ChoBeomGyu25/2026ESWContest_free_-/SW/Jetson/preprocessing/lower/dual/undistort/step_d25_v2.py

#!/usr/bin/env python3
# -*- coding: utf-8 -*-
"""
step_d25.py

Reference-free bottom/pants finish evaluator.

This file never opens RoArm serial ports and never sends robot commands.
It combines the YOLO26m bottom-pose engine, segmentation contour derivatives,
convexity defects and pose-relative topology to evaluate:

  1) one coherent waist region,
  2) one expected crotch concavity,
  3) two exposed legs and two visible hems,
  4) pose/geometry-fused eight keypoints,
  5) unexpected macro boundary folds or overlap,
  6) broad contrast-supported internal folds only.

No per-garment normal image or user registration is used. Fine wrinkles, elastic
waist gathers, center-rise seams and ordinary hem lines do not block finish.

Snapshot keys:
  Q / ESC : quit
  SPACE   : force one fresh snapshot and evaluate it
  C       : clear the frozen result
  L       : lock/update Homography from currently detected ArUco markers
  R       : clear Homography in memory
  S       : save current overlay and JSON report

Dependency:
  Keep step_d23_v2.py in the same directory.

Recommended:
  python3 step_d25.py

No-window one-shot snapshot:
  python3 step_d25.py --once --no-window
"""

from __future__ import annotations

import argparse
import collections
import json
import math
import os
import sys
import threading
import time
from dataclasses import dataclass, field
from pathlib import Path
from types import SimpleNamespace
from typing import Any, Deque, Dict, List, Optional, Sequence, Tuple

import cv2
import numpy as np

try:
    import step_d23_v2 as d23
except Exception as exc:  # pragma: no cover - clear runtime error for Jetson use
    raise RuntimeError(
        "step_d25.py requires step_d23_v2.py in the same directory. "
        f"Import failed: {exc!r}"
    ) from exc


STEP_D24_BUILD = "2026-07-17-d25-contour-differential-topology-medium-pose"

STATUS_COLORS = {
    "REJUDGE": (0, 190, 255),
    "NOT_READY_SHAPE": (0, 0, 255),
    "NOT_READY_WRINKLE": (0, 80, 255),
    "READY_PENDING": (0, 220, 220),
    "READY_GOOD_ENOUGH": (0, 210, 0),
}

TIER_COLORS = {
    1: (255, 170, 40),   # blue-ish: allowed fine wrinkle
    2: (0, 165, 255),    # orange
    3: (0, 0, 255),      # red
}


@dataclass
class StabilityEntry:
    timestamp: float
    mask_area_px: float
    mask_center_board: np.ndarray
    pose_axis_deg: float
    valid_kpts: int
    mean_kpt_conf: float


@dataclass
class D24State:
    history: Deque[StabilityEntry]
    ready_streak: int = 0
    evaluation_count: int = 0
    latest_status: str = "REJUDGE"
    latest_report: Dict[str, Any] = field(default_factory=dict)
    latest_obs: Optional[Any] = None
    latest_heat: Optional[Any] = None
    latest_overlay: Optional[np.ndarray] = None
    latest_eval_frame: Optional[np.ndarray] = None
    latest_h: Optional[np.ndarray] = None
    last_eval_started: float = 0.0
    force_evaluate: bool = False
    paused: bool = False

    def reset_temporal(self) -> None:
        self.history.clear()
        self.ready_streak = 0
        self.latest_status = "REJUDGE"
        self.latest_report = {
            "status": "REJUDGE",
            "reason": "temporal history reset",
        }


# -----------------------------------------------------------------------------
# Argument/config construction
# -----------------------------------------------------------------------------

def build_parser() -> argparse.ArgumentParser:
    p = argparse.ArgumentParser(
        description="D24-v6 event snapshot tester: pants shape + real-fold-only finish + waist/gather/center-rise structure ignore; no robot motion"
    )

    # Camera / files.
    p.add_argument("--config", default="dual_roarm_big_table_config.json")
    p.add_argument("--hfile", default="dual_big_table_homography_cache.json")
    p.add_argument("--load-h", dest="load_h", action="store_true", default=True)
    p.add_argument("--no-load-h", dest="load_h", action="store_false")
    p.add_argument("--save-h-on-lock", dest="save_h_on_lock", action="store_true", default=True)
    p.add_argument("--no-save-h-on-lock", dest="save_h_on_lock", action="store_false")
    p.add_argument("--auto-lock", dest="auto_lock", action="store_true", default=True)
    p.add_argument("--no-auto-lock", dest="auto_lock", action="store_false")

    p.add_argument("--camera", type=int, default=0)
    p.add_argument("--width", type=int, default=1280)
    p.add_argument("--height", type=int, default=720)
    p.add_argument("--backend", choices=["auto", "v4l2", "dshow", "any"], default="v4l2")
    p.add_argument("--cam-device", default="")
    p.add_argument("--cam-exposure-abs", type=int, default=35)
    p.add_argument("--cam-gain", type=int, default=5)
    p.add_argument("--cam-no-manual", action="store_true")
    p.add_argument("--cam-auto-adjust", dest="cam_auto_adjust", action="store_true", default=False)
    p.add_argument("--cam-auto-settle-s", type=float, default=0.40)
    p.add_argument("--cam-auto-exposure-min", type=int, default=10)
    p.add_argument("--cam-auto-exposure-max", type=int, default=100)
    p.add_argument("--cam-auto-gain-min", type=int, default=0)
    p.add_argument("--cam-auto-gain-max", type=int, default=20)
    p.add_argument("--warmup-frames", type=int, default=10)
    p.add_argument("--no-window", action="store_true")
    p.add_argument("--once", action="store_true")
    p.add_argument("--image", default="", help="Evaluate one saved image instead of the camera.")
    p.add_argument("--output", default="d25_finish_overlay.jpg")
    p.add_argument("--snapshot-dir", default="d25_finish_samples")
    p.add_argument("--log-jsonl", default="d25_finish_log.jsonl")

    # Models and pose inference.
    p.add_argument(
        "--seg-model",
        default="/workspace/project_train/aruco_test/dual/models/kfashion_yolo26s_seg3_e100_best.engine",
    )
    p.add_argument("--seg-imgsz", type=int, default=640)
    p.add_argument("--seg-conf", type=float, default=0.25)
    p.add_argument(
        "--pose-model",
        default="/workspace/project_train/yolo26/bottom_pose8_yolo26m_e40_best.engine",
    )
    p.add_argument("--pose-imgsz", type=int, default=640)
    p.add_argument("--pose-conf", type=float, default=0.10)
    p.add_argument("--pose-kpt-conf", type=float, default=0.20)
    p.add_argument("--pose-tta", dest="pose_tta", action="store_true", default=True)
    p.add_argument("--no-pose-tta", dest="pose_tta", action="store_false")
    p.add_argument("--angles", default="0,180,90,-90,45,-45")
    p.add_argument("--flip-modes", default="none,h")

    # Staged TTA from D23: fast common orientations, full fallback only if weak.
    p.add_argument("--d23-pose-tta-fast-first", dest="d23_pose_tta_fast_first", action="store_true", default=True)
    p.add_argument("--no-d23-pose-tta-fast-first", dest="d23_pose_tta_fast_first", action="store_false")
    p.add_argument("--d23-pose-tta-fast-angles", default="0,180")
    p.add_argument("--d23-pose-tta-fast-flip-modes", default="none")
    p.add_argument("--d23-pose-tta-fast-min-score", type=float, default=28.0)
    p.add_argument("--d23-pose-tta-fast-min-visible", type=int, default=7)
    p.add_argument("--d23-pose-tta-fast-min-mean-conf", type=float, default=0.32)

    # Pose TTA geometry and mask fallback.
    p.add_argument("--tta-min-waist-width-px", type=float, default=40.0)
    p.add_argument("--tta-max-waist-center-offset-ratio", type=float, default=0.35)
    p.add_argument("--tta-min-waist-to-crotch-ratio", type=float, default=0.35)
    p.add_argument("--tta-max-waist-axis-dot", type=float, default=0.45)
    p.add_argument("--tta-pre-spread-hem-gap-ratio", type=float, default=0.42)
    p.add_argument("--tta-pre-spread-open-angle-deg", type=float, default=22.0)
    p.add_argument("--tta-pre-spread-min-hem-visible", type=int, default=2)
    p.add_argument("--tta-mask-max-outside-px", type=float, default=28.0)
    p.add_argument("--tta-mask-min-inside-ratio", type=float, default=0.60)
    p.add_argument("--tta-require-ok-for-motion", dest="tta_require_ok_for_motion", action="store_true", default=True)
    p.add_argument("--no-tta-require-ok-for-motion", dest="tta_require_ok_for_motion", action="store_false")

    p.add_argument("--pose-grabcut-fallback", dest="pose_grabcut_fallback", action="store_true", default=True)
    p.add_argument("--no-pose-grabcut-fallback", dest="pose_grabcut_fallback", action="store_false")
    p.add_argument("--fallback-mask-min-pose-points", type=int, default=6)
    p.add_argument("--fallback-mask-bbox-pad-px", type=int, default=55)
    p.add_argument("--fallback-mask-seed-radius-px", type=int, default=12)
    p.add_argument("--fallback-mask-seed-line-px", type=int, default=18)
    p.add_argument("--fallback-mask-hull-dilate-px", type=int, default=28)
    p.add_argument("--fallback-mask-grabcut-iters", type=int, default=4)
    p.add_argument("--fallback-mask-close-px", type=int, default=9)
    p.add_argument("--fallback-mask-open-px", type=int, default=3)
    p.add_argument("--fallback-mask-min-area-px", type=float, default=1800.0)
    p.add_argument("--fallback-mask-max-frame-ratio", type=float, default=0.70)
    p.add_argument("--fallback-mask-max-kpt-outside-px", type=float, default=22.0)
    p.add_argument("--fallback-mask-min-inside-points", type=int, default=6)
    p.add_argument("--fallback-mask-min-solidity", type=float, default=0.35)

    # Continuous evaluation and temporal stability.
    p.add_argument("--eval-interval-s", type=float, default=0.75)
    p.add_argument("--burst-frame-count", type=int, default=5)
    p.add_argument("--history-count", type=int, default=3)
    p.add_argument("--ready-confirm-count", type=int, default=2)
    p.add_argument("--min-valid-keypoints", type=int, default=7)
    p.add_argument("--min-mean-kpt-conf", type=float, default=0.45)
    p.add_argument("--stable-mask-area-rel", type=float, default=0.05)
    p.add_argument("--stable-center-shift-mm", type=float, default=8.0)
    p.add_argument("--stable-pose-axis-spread-deg", type=float, default=6.0)

    # Base heatmap.
    p.add_argument("--wrinkle-heatmap-mode", dest="wrinkle_heatmap_mode", action="store_true", default=True)
    p.add_argument("--no-wrinkle-heatmap-mode", dest="wrinkle_heatmap_mode", action="store_false")
    p.add_argument("--wrinkle-heatmap-draw", dest="wrinkle_heatmap_draw", action="store_true", default=True)
    p.add_argument("--no-wrinkle-heatmap-draw", dest="wrinkle_heatmap_draw", action="store_false")
    p.add_argument("--wrinkle-heatmap-alpha", type=float, default=0.30)
    p.add_argument("--wrinkle-heatmap-clahe-clip", type=float, default=2.0)
    p.add_argument("--wrinkle-heatmap-clahe-tile", type=int, default=8)
    p.add_argument("--wrinkle-heatmap-blur-ksize", type=int, default=41)
    p.add_argument("--wrinkle-heatmap-erode-px", type=int, default=12)
    p.add_argument("--wrinkle-heatmap-percentile", type=float, default=93.0)
    p.add_argument("--wrinkle-heatmap-min-blob-area", type=float, default=45.0)
    p.add_argument("--wrinkle-heatmap-max-candidates", type=int, default=12)
    p.add_argument("--wrinkle-heatmap-gabor", dest="wrinkle_heatmap_gabor", action="store_true", default=True)
    p.add_argument("--no-wrinkle-heatmap-gabor", dest="wrinkle_heatmap_gabor", action="store_false")
    p.add_argument("--wrinkle-heatmap-gabor-ksize", type=int, default=17)
    p.add_argument("--wrinkle-heatmap-gabor-lambda", type=float, default=8.0)
    p.add_argument("--wrinkle-heatmap-gabor-sigma", type=float, default=4.0)
    p.add_argument("--wrinkle-heatmap-score-min", type=float, default=35.0)

    # D24 robust response guard. This supplements P93 rather than allowing P93 alone.
    p.add_argument("--d24-robust-k", type=float, default=2.7)
    p.add_argument("--d24-robust-score-min", type=float, default=35.0)
    p.add_argument("--d24-candidate-min-robust-support", type=float, default=0.10)

    # Natural structure ignore zones.
    p.add_argument("--d19-ignore-waistband-wrinkles", dest="d19_ignore_waistband_wrinkles", action="store_true", default=True)
    p.add_argument("--no-d19-ignore-waistband-wrinkles", dest="d19_ignore_waistband_wrinkles", action="store_false")
    p.add_argument("--d19-waistband-back-mm", type=float, default=18.0)
    p.add_argument("--d19-waistband-forward-mm", type=float, default=72.0)
    p.add_argument("--d19-waistband-side-expand-mm", type=float, default=28.0)
    p.add_argument("--d23-waistband-forward-ratio", type=float, default=0.70)
    p.add_argument("--d23-waistband-forward-max-mm", type=float, default=95.0)
    p.add_argument("--d23-waist-structure-veto", dest="d23_waist_structure_veto", action="store_true", default=True)
    p.add_argument("--no-d23-waist-structure-veto", dest="d23_waist_structure_veto", action="store_false")
    p.add_argument("--d23-waist-structure-back-mm", type=float, default=22.0)
    p.add_argument("--d23-waist-structure-forward-mm", type=float, default=78.0)
    p.add_argument("--d23-waist-structure-forward-ratio", type=float, default=0.70)
    p.add_argument("--d23-waist-structure-forward-max-mm", type=float, default=98.0)
    p.add_argument("--d23-waist-structure-side-expand-mm", type=float, default=32.0)
    p.add_argument("--d23-waist-structure-parallel-deg", type=float, default=25.0)
    p.add_argument("--d23-waist-structure-min-length-mm", type=float, default=35.0)
    p.add_argument("--d23-waist-structure-min-length-ratio", type=float, default=0.22)
    p.add_argument("--d23-pre-veto-candidate-multiplier", type=int, default=3)
    p.add_argument("--d23-draw-waist-veto", dest="d23_draw_waist_veto", action="store_true", default=True)
    p.add_argument("--no-d23-draw-waist-veto", dest="d23_draw_waist_veto", action="store_false")

    p.add_argument("--d19-ignore-crotch-wrinkles", dest="d19_ignore_crotch_wrinkles", action="store_true", default=True)
    p.add_argument("--no-d19-ignore-crotch-wrinkles", dest="d19_ignore_crotch_wrinkles", action="store_false")
    p.add_argument("--d19-crotch-axial-radius-mm", type=float, default=56.0)
    p.add_argument("--d19-crotch-lateral-radius-mm", type=float, default=66.0)
    p.add_argument("--d19-crotch-forward-shift-mm", type=float, default=10.0)

    # Conditional seam veto: do not erase the entire side/hem area; require line agreement.
    p.add_argument("--d24-seam-veto", dest="d24_seam_veto", action="store_true", default=True)
    p.add_argument("--no-d24-seam-veto", dest="d24_seam_veto", action="store_false")
    p.add_argument("--d24-seam-band-mm", type=float, default=18.0)
    p.add_argument("--d24-seam-parallel-deg", type=float, default=24.0)
    p.add_argument("--d24-seam-min-linearity", type=float, default=3.0)
    p.add_argument("--d24-seam-min-length-mm", type=float, default=30.0)
    p.add_argument("--d24-seam-min-support-ratio", type=float, default=0.70)
    p.add_argument("--d24-seam-max-sample-points", type=int, default=1800)

    # D20 meaningful wrinkle classification.
    p.add_argument("--d20-require-dark-shadow", dest="d20_require_dark_shadow", action="store_true", default=True)
    p.add_argument("--no-d20-require-dark-shadow", dest="d20_require_dark_shadow", action="store_false")
    p.add_argument("--d20-ignore-fine-wrinkles", dest="d20_ignore_fine_wrinkles", action="store_true", default=True)
    p.add_argument("--no-d20-ignore-fine-wrinkles", dest="d20_ignore_fine_wrinkles", action="store_false")
    p.add_argument("--d20-shadow-blur-ksize", type=int, default=51)
    p.add_argument("--d20-shadow-min-scale-raw", type=float, default=8.0)
    p.add_argument("--d20-shadow-support-raw-min", type=float, default=3.0)
    p.add_argument("--d20-hard-min-component-area-px", type=float, default=70.0)

    # T3 strong criteria.
    p.add_argument("--d20-strong-area-px", type=float, default=240.0)
    p.add_argument("--d20-strong-area-ratio", type=float, default=0.015)
    p.add_argument("--d20-strong-length-mm", type=float, default=80.0)
    p.add_argument("--d20-strong-length-px", type=float, default=95.0)
    p.add_argument("--d20-strong-dark-mean", type=float, default=38.0)
    p.add_argument("--d20-strong-dark-max", type=float, default=105.0)
    p.add_argument("--d20-strong-dark-support", type=float, default=0.10)

    # T2 medium criteria.
    p.add_argument("--d20-medium-area-px", type=float, default=150.0)
    p.add_argument("--d20-medium-area-ratio", type=float, default=0.005)
    p.add_argument("--d20-medium-length-mm", type=float, default=45.0)
    p.add_argument("--d20-medium-length-px", type=float, default=58.0)
    p.add_argument("--d20-medium-dark-mean", type=float, default=20.0)
    p.add_argument("--d20-medium-dark-max", type=float, default=65.0)
    p.add_argument("--d20-medium-dark-support", type=float, default=0.06)

    # D21 candidate severity / T1 allowance.
    p.add_argument("--d21v4-action-min-tier", type=int, default=2)
    p.add_argument("--d21v4-action-severity-override", type=float, default=0.55)
    p.add_argument("--d21v4-good-enough-finish", dest="d21v4_good_enough_finish", action="store_true", default=True)
    p.add_argument("--d21-severity-length-ref-mm", type=float, default=120.0)
    p.add_argument("--d21-severity-area-ref-px", type=float, default=550.0)
    p.add_argument("--d21-severity-dark-ref", type=float, default=60.0)
    p.add_argument("--d21-severity-dark-max-ref", type=float, default=160.0)
    p.add_argument("--d21-severity-sagitta-ref-mm", type=float, default=45.0)
    p.add_argument("--d21-pull-min-mm", type=float, default=25.0)
    p.add_argument("--d21-pull-max-mm", type=float, default=95.0)

    # Shape thresholds from the agreed algorithm.
    p.add_argument("--finish-shape-score-min", type=float, default=0.75)
    p.add_argument("--finish-hem-gap-ratio-min", type=float, default=0.55)
    p.add_argument("--finish-hem-gap-ratio-max", type=float, default=1.35)
    p.add_argument("--finish-leg-balance-min", type=float, default=0.82)
    p.add_argument("--finish-waist-center-offset-max", type=float, default=0.15)
    p.add_argument("--finish-waist-line-error-max", type=float, default=0.16)
    p.add_argument("--finish-crotch-axis-offset-max", type=float, default=0.22)
    p.add_argument("--finish-axis-to-waist-min", type=float, default=0.75)

    # Lower silhouette thresholds.
    p.add_argument("--d22-require-lower-leg-symmetry", dest="d22_require_lower_leg_symmetry", action="store_true", default=True)
    p.add_argument("--no-d22-require-lower-leg-symmetry", dest="d22_require_lower_leg_symmetry", action="store_false")
    p.add_argument("--d22-symmetry-axis-min-mm", type=float, default=35.0)
    p.add_argument("--d22-symmetry-lower-start-mm", type=float, default=-4.0)
    p.add_argument("--d22-symmetry-ignore-axis-band-mm", type=float, default=5.0)
    p.add_argument("--d22-symmetry-grid-mm", type=float, default=4.0)
    p.add_argument("--d22-symmetry-grid-close-cells", type=int, default=1)
    p.add_argument("--d22-symmetry-band-count", type=int, default=6)
    p.add_argument("--d22-symmetry-min-points-per-band", type=int, default=60)
    p.add_argument("--d22-symmetry-max-sample-points", type=int, default=100000)
    p.add_argument("--d22-lower-reflected-iou-min", type=float, default=0.68)
    p.add_argument("--d22-lower-width-balance-median-min", type=float, default=0.75)
    p.add_argument("--d22-lower-width-balance-min-min", type=float, default=0.60)
    p.add_argument("--d22-lower-profile-error-p90-max", type=float, default=0.38)
    p.add_argument("--d22-lower-side-area-balance-min", type=float, default=0.74)
    p.add_argument("--d22-hem-axis-balance-min", type=float, default=0.74)
    p.add_argument("--d22-leg-length-balance-min", type=float, default=0.82)
    p.add_argument("--d22-symmetry-score-min", type=float, default=0.70)

    # D24-v2 final policy: pants shape is mandatory, but only clearly major
    # wrinkles block READY. T1/T2 counts and total active ratio are diagnostic only.
    p.add_argument("--finish-max-t3-count", type=int, default=0)
    p.add_argument("--finish-max-t2-count", type=int, default=999)  # display/compatibility only
    p.add_argument("--finish-max-severity", type=float, default=1.0)  # display/compatibility only
    p.add_argument("--finish-actionable-ratio", type=float, default=1.0)  # diagnostic only
    p.add_argument("--finish-max-blob-ratio", type=float, default=1.0)  # diagnostic only

    # Waistline-relative fine-wrinkle allowance. A candidate smaller/weaker than
    # the detected waistband structure is explicitly marked as allowed.
    p.add_argument("--d24v2-waist-relative-enable", dest="d24v2_waist_relative_enable", action="store_true", default=True)
    p.add_argument("--no-d24v2-waist-relative-enable", dest="d24v2_waist_relative_enable", action="store_false")
    p.add_argument("--d24v2-waist-length-ratio-ignore", type=float, default=0.40)
    p.add_argument("--d24v2-waist-area-ratio-ignore", type=float, default=0.30)
    p.add_argument("--d24v2-waist-response-ratio-ignore", type=float, default=0.85)
    p.add_argument("--d24v2-waist-ref-back-mm", type=float, default=18.0)
    p.add_argument("--d24v2-waist-ref-forward-mm", type=float, default=72.0)
    p.add_argument("--d24v2-waist-ref-side-expand-mm", type=float, default=28.0)
    p.add_argument("--d24v2-waist-ref-parallel-deg", type=float, default=30.0)
    p.add_argument("--d24v2-waist-ref-min-length-ratio", type=float, default=0.25)
    p.add_argument("--d24v2-waist-ref-min-area-px", type=float, default=45.0)
    p.add_argument("--d24v2-waist-ref-threshold-scale", type=float, default=0.78)

    # Absolute major-wrinkle overrides. These block READY even when the candidate
    # is smaller than the waistband reference.
    p.add_argument("--d24v2-major-length-mm", type=float, default=80.0)
    p.add_argument("--d24v2-major-area-ratio", type=float, default=0.015)
    p.add_argument("--d24v2-major-severity", type=float, default=0.60)
    p.add_argument("--d24v2-major-severity-min-length-mm", type=float, default=60.0)
    p.add_argument("--d24v2-major-waist-span-ratio", type=float, default=0.50)
    p.add_argument("--d24v2-major-waist-span-min-area-ratio", type=float, default=0.005)

    # D24-v5: waistband-connected radial gathers are natural elastic-waist structures.
    p.add_argument("--d24v5-waist-gather-ignore", dest="d24v5_waist_gather_ignore", action="store_true", default=True)
    p.add_argument("--no-d24v5-waist-gather-ignore", dest="d24v5_waist_gather_ignore", action="store_false")
    p.add_argument("--d24v5-waist-gather-depth-ratio", type=float, default=0.45,
                   help="Maximum gather depth as a fraction of waist-to-crotch distance.")
    p.add_argument("--d24v5-waist-gather-depth-max-mm", type=float, default=105.0)
    p.add_argument("--d24v5-waist-gather-connect-mm", type=float, default=22.0,
                   help="Allowed gap from the existing waistband ignore boundary.")
    p.add_argument("--d24v5-waist-gather-radial-angle-deg", type=float, default=32.0)
    p.add_argument("--d24v5-waist-gather-max-length-ratio", type=float, default=0.35)
    p.add_argument("--d24v5-waist-gather-max-length-mm", type=float, default=78.0)
    p.add_argument("--d24v5-waist-gather-max-area-ratio", type=float, default=0.012)
    p.add_argument("--d24v5-waist-gather-side-expand-mm", type=float, default=20.0)
    p.add_argument("--d24v5-waist-gather-min-upper-support", type=float, default=0.70)

    # D24-v5: fine wrinkles never block finish. Only broad/deep fold-like components do.
    p.add_argument("--d24v5-fold-min-length-mm", type=float, default=75.0)
    p.add_argument("--d24v5-fold-min-width-mm", type=float, default=7.0)
    p.add_argument("--d24v5-fold-min-area-ratio", type=float, default=0.0045)
    p.add_argument("--d24v5-fold-min-severity", type=float, default=0.45)
    p.add_argument("--d24v5-fold-min-mean-response", type=float, default=75.0)
    p.add_argument("--d24v5-fold-broad-min-length-mm", type=float, default=45.0)
    p.add_argument("--d24v5-fold-broad-min-width-mm", type=float, default=13.0)
    p.add_argument("--d24v5-fold-broad-min-area-ratio", type=float, default=0.0075)
    p.add_argument("--d24v5-fold-large-area-ratio", type=float, default=0.018)
    p.add_argument("--d24v5-draw-allowed-fine", dest="d24v5_draw_allowed_fine", action="store_true", default=False)
    p.add_argument("--no-d24v5-draw-allowed-fine", dest="d24v5_draw_allowed_fine", action="store_false")

    # D24-v6: pose-relative front/center-rise seam from waist center toward crotch.
    # This narrow structure band is erased BEFORE CCA so a bright seam cannot merge
    # with nearby waistband gathers and become one large false fold component.
    p.add_argument("--d24v6-center-rise-ignore", dest="d24v6_center_rise_ignore", action="store_true", default=True)
    p.add_argument("--no-d24v6-center-rise-ignore", dest="d24v6_center_rise_ignore", action="store_false")
    p.add_argument("--d24v6-center-rise-half-width-mm", type=float, default=18.0)
    p.add_argument("--d24v6-center-rise-start-mm", type=float, default=48.0,
                   help="Distance below waist center where the narrow center-rise seam mask starts.")
    p.add_argument("--d24v6-center-rise-end-before-crotch-mm", type=float, default=0.0)
    p.add_argument("--d24v6-center-rise-end-expand-mm", type=float, default=12.0)

    # D24-v6 color-robust fold gate. A large normalized heatmap component alone is
    # no longer a blocker; broad geometry must also have real local intensity contrast.
    p.add_argument("--d24v6-fold-min-abs-contrast", type=float, default=7.0,
                   help="Minimum mean absolute high-pass contrast in original gray levels.")
    p.add_argument("--d24v6-fold-min-contrast-support", type=float, default=0.28,
                   help="Minimum fraction of component pixels above the absolute-contrast pixel threshold.")
    p.add_argument("--d24v6-fold-contrast-pixel-threshold", type=float, default=8.0)
    p.add_argument("--d24v6-fold-extreme-width-mm", type=float, default=22.0)
    p.add_argument("--d24v6-fold-extreme-area-ratio", type=float, default=0.016)

    # D24-v4 event-driven snapshot gate. The camera remains live, but heavy
    # pose/segmentation/heatmap inference runs only after a confirmed scene change
    # followed by a stillness interval.
    p.add_argument("--auto-snapshot-on-change", dest="auto_snapshot_on_change", action="store_true", default=True)
    p.add_argument("--no-auto-snapshot-on-change", dest="auto_snapshot_on_change", action="store_false")
    p.add_argument("--startup-auto-snapshot", dest="startup_auto_snapshot", action="store_true", default=True)
    p.add_argument("--no-startup-auto-snapshot", dest="startup_auto_snapshot", action="store_false")
    p.add_argument("--change-mean-threshold", type=float, default=3.5,
                   help="Brightness-compensated mean board difference needed to arm a new snapshot.")
    p.add_argument("--change-pixel-threshold", type=float, default=12.0,
                   help="Per-pixel difference used to calculate changed-area ratio.")
    p.add_argument("--change-active-ratio", type=float, default=0.018,
                   help="Fraction of board pixels that must change when mean difference alone is small.")
    p.add_argument("--change-min-frames", type=int, default=3,
                   help="Consecutive changed frames required before waiting for stillness.")
    p.add_argument("--change-cooldown-s", type=float, default=0.60,
                   help="Ignore change triggers briefly after each completed snapshot.")
    p.add_argument("--change-board-shrink-px", type=int, default=10,
                   help="Ignore a narrow band at the ArUco board boundary during change detection.")
    p.add_argument("--change-preview-width", type=int, default=160)
    p.add_argument("--change-preview-height", type=int, default=90)
    p.add_argument("--settle-motion-threshold", type=float, default=2.5,
                   help="Frame-to-frame mean difference below which the pants are considered still.")
    p.add_argument("--settle-seconds", type=float, default=0.80,
                   help="How long the view must remain still before automatic snapshot inference.")
    p.add_argument("--settle-min-frames", type=int, default=5)
    p.add_argument("--capture-flush-frames", type=int, default=2)
    p.add_argument("--pause-auto", dest="pause_auto", action="store_true", default=False)

    p.add_argument("--panel-width", type=int, default=680)
    p.add_argument("--window-name", default="D25_PANTS_TOPOLOGY_FINISH")
    return p


def finalize_args(args: argparse.Namespace) -> argparse.Namespace:
    args.pose_tta_angles_list = d23.parse_pose_tta_angles(args.angles)
    args.pose_tta_flip_modes_list = d23.parse_pose_tta_flip_modes(args.flip_modes)

    # Names expected by D23 shape helpers.
    args.d19_finish_require_shape = True
    args.d19_finish_shape_score_good = float(args.finish_shape_score_min)
    args.d19_finish_shape_hem_gap_ratio_min = float(args.finish_hem_gap_ratio_min)
    args.d19_finish_shape_hem_gap_ratio_max = float(args.finish_hem_gap_ratio_max)
    args.d19_finish_shape_leg_balance_min = float(args.finish_leg_balance_min)
    args.d19_finish_shape_waist_center_offset_max = float(args.finish_waist_center_offset_max)
    args.d19_finish_shape_waist_line_error_max = float(args.finish_waist_line_error_max)
    args.d19_finish_shape_crotch_axis_offset_max = float(args.finish_crotch_axis_offset_max)
    args.d19_finish_shape_axis_to_waist_min = float(args.finish_axis_to_waist_min)

    # Geometry helper defaults that are accessed directly in a few old functions.
    args.d21_curve_min_inlier_ratio = 0.62
    args.d21_curve_max_residual_mm = 8.0
    args.d21_curve_min_sagitta_mm = 10.0
    args.d21_curve_min_arc_length_mm = 50.0
    args.d21_curve_min_radius_mm = 25.0
    args.d21_curve_max_radius_mm = 900.0
    args.d21_curve_vs_line_error_ratio = 0.90
    args.d21_line_max_residual_mm = 8.0
    args.d21_line_max_sagitta_mm = 10.0
    args.d21_circle_ransac_iters = 120
    args.d21_circle_inlier_tol_mm = 7.0
    args.d21_fit_max_points = 220
    args.d21_track_match_distance_mm = 35.0
    args.d21_static_required_actions = 999999  # No automatic structural learning in D24.
    args.d21v3_static_require_fine = True
    args.d21v3_static_max_tier = 1
    args.d21v3_static_max_severity = 0.45
    args.d21v3_static_max_length_mm = 65.0
    args.d21v3_static_max_area_px = 240.0
    args.d21v3_static_max_dark_mean = 38.0
    return args


# -----------------------------------------------------------------------------
# Geometry / temporal stability
# -----------------------------------------------------------------------------

def angle_diff_180(a_deg: float, b_deg: float) -> float:
    return abs((float(a_deg) - float(b_deg) + 90.0) % 180.0 - 90.0)


def pose_axis_angle(obs: Any) -> float:
    if obs is None or obs.pose is None:
        return 0.0
    v = np.asarray(obs.pose.lower_center, np.float32) - np.asarray(obs.pose.waist_center, np.float32)
    return float(math.degrees(math.atan2(float(v[1]), float(v[0]))))


def observation_entry(obs: Any) -> StabilityEntry:
    confs = list(obs.pose.keypoint_conf.values()) if obs and obs.pose else []
    return StabilityEntry(
        timestamp=time.time(),
        mask_area_px=float(obs.mask.area_px),
        mask_center_board=np.asarray(obs.mask.center_board, np.float32).reshape(2),
        pose_axis_deg=pose_axis_angle(obs),
        valid_kpts=len(confs),
        mean_kpt_conf=float(np.mean(confs)) if confs else 0.0,
    )


def temporal_stability_report(history: Sequence[StabilityEntry], args) -> Dict[str, Any]:
    need = max(2, int(args.history_count))
    if len(history) < need:
        return {
            "good": False,
            "reason": f"history {len(history)}/{need}",
            "history_count": len(history),
            "required": need,
        }

    entries = list(history)[-need:]
    areas = np.asarray([e.mask_area_px for e in entries], np.float32)
    centers = np.asarray([e.mask_center_board for e in entries], np.float32)
    angles = [e.pose_axis_deg for e in entries]

    med_area = float(np.median(areas))
    area_rel = float(np.max(np.abs(areas - med_area)) / max(1.0, med_area))
    med_center = np.median(centers, axis=0)
    center_shift = float(np.max(np.linalg.norm(centers - med_center.reshape(1, 2), axis=1)))
    angle_spread = max(angle_diff_180(a, b) for a in angles for b in angles)

    checks = {
        "mask_area": area_rel <= float(args.stable_mask_area_rel),
        "mask_center": center_shift <= float(args.stable_center_shift_mm),
        "pose_axis": angle_spread <= float(args.stable_pose_axis_spread_deg),
    }
    return {
        "good": bool(all(checks.values())),
        "reason": "OK" if all(checks.values()) else "observation changed",
        "checks": checks,
        "history_count": len(entries),
        "mask_area_rel": area_rel,
        "center_shift_mm": center_shift,
        "pose_axis_spread_deg": float(angle_spread),
        "limits": {
            "mask_area_rel": float(args.stable_mask_area_rel),
            "center_shift_mm": float(args.stable_center_shift_mm),
            "pose_axis_spread_deg": float(args.stable_pose_axis_spread_deg),
        },
    }


# -----------------------------------------------------------------------------
# Conditional side/inner/hem seam filtering
# -----------------------------------------------------------------------------

def point_segment_distances(points: np.ndarray, a: np.ndarray, b: np.ndarray) -> np.ndarray:
    pts = np.asarray(points, np.float32).reshape(-1, 2)
    a = np.asarray(a, np.float32).reshape(2)
    b = np.asarray(b, np.float32).reshape(2)
    ab = b - a
    denom = float(np.dot(ab, ab))
    if denom < 1e-8:
        return np.linalg.norm(pts - a.reshape(1, 2), axis=1)
    t = np.clip(((pts - a.reshape(1, 2)) @ ab) / denom, 0.0, 1.0)
    proj = a.reshape(1, 2) + t[:, None] * ab.reshape(1, 2)
    return np.linalg.norm(pts - proj, axis=1)


def expected_seam_segments(obs: Any) -> List[Dict[str, Any]]:
    if obs is None or obs.pose is None:
        return []
    kb = obs.pose.keypoints_board
    segments: List[Dict[str, Any]] = []

    def add(name: str, n1: str, n2: str) -> None:
        if n1 in kb and n2 in kb:
            a = np.asarray(kb[n1], np.float32)
            b = np.asarray(kb[n2], np.float32)
            if float(np.linalg.norm(b - a)) >= 12.0:
                segments.append({"name": name, "a": a, "b": b})

    add("LEFT_OUTER_SEAM", "waist_img_left", "img_left_hem_outer")
    add("RIGHT_OUTER_SEAM", "waist_img_right", "img_right_hem_outer")
    add("LEFT_INNER_SEAM", "crotch", "img_left_hem_inner")
    add("RIGHT_INNER_SEAM", "crotch", "img_right_hem_inner")
    add("LEFT_HEM", "img_left_hem_outer", "img_left_hem_inner")
    add("RIGHT_HEM", "img_right_hem_inner", "img_right_hem_outer")
    return segments


def candidate_component_mask(heat: Any, cand: Dict[str, Any]) -> Optional[np.ndarray]:
    binary = getattr(heat, "d21v4_residual_binary", None)
    if not isinstance(binary, np.ndarray):
        binary = getattr(heat, "binary", None)
    if not isinstance(binary, np.ndarray):
        return None
    n, labels = cv2.connectedComponents((binary > 0).astype(np.uint8), connectivity=8)
    cx, cy = [int(round(float(v))) for v in cand.get("center_px", [0.0, 0.0])]
    cx = int(np.clip(cx, 0, labels.shape[1] - 1))
    cy = int(np.clip(cy, 0, labels.shape[0] - 1))
    lid = int(labels[cy, cx])
    if lid <= 0 or lid >= n:
        # Search within the candidate bbox if its center fell in a morphology hole.
        x, y, w, h = [int(v) for v in cand.get("bbox", [0, 0, 0, 0])]
        roi = labels[max(0, y):min(labels.shape[0], y + h), max(0, x):min(labels.shape[1], x + w)]
        vals, counts = np.unique(roi[roi > 0], return_counts=True)
        if len(vals) == 0:
            return None
        lid = int(vals[int(np.argmax(counts))])
    return ((labels == lid).astype(np.uint8) * 255)


def component_board_points(component: np.ndarray, H: np.ndarray, max_points: int) -> np.ndarray:
    ys, xs = np.where(component > 0)
    pts = np.column_stack([xs, ys]).astype(np.float32)
    if len(pts) > max_points:
        step = max(1, int(math.ceil(len(pts) / float(max_points))))
        pts = pts[::step]
    if len(pts) == 0:
        return np.empty((0, 2), np.float32)
    return cv2.perspectiveTransform(pts.reshape(-1, 1, 2), H).reshape(-1, 2)


def axis_angle_error_deg(v1: np.ndarray, v2: np.ndarray) -> float:
    a = np.asarray(v1, np.float32).reshape(2)
    b = np.asarray(v2, np.float32).reshape(2)
    na, nb = float(np.linalg.norm(a)), float(np.linalg.norm(b))
    if na < 1e-6 or nb < 1e-6:
        return 180.0
    c = float(np.clip(abs(np.dot(a / na, b / nb)), 0.0, 1.0))
    return float(math.degrees(math.acos(c)))


def seam_veto_report(cand: Dict[str, Any], heat: Any, obs: Any, H: np.ndarray, args) -> Dict[str, Any]:
    out: Dict[str, Any] = {"matched": False, "name": "", "reason": "not a seam"}
    if not bool(args.d24_seam_veto):
        return out

    length = float(cand.get("major_length_mm", 0.0))
    linearity = float(cand.get("linearity", 1.0))
    if length < float(args.d24_seam_min_length_mm) or linearity < float(args.d24_seam_min_linearity):
        return {**out, "reason": "short or non-linear"}

    comp = candidate_component_mask(heat, cand)
    if comp is None:
        return {**out, "reason": "component unavailable"}
    pts = component_board_points(comp, H, max(100, int(args.d24_seam_max_sample_points)))
    if len(pts) < 8:
        return {**out, "reason": "too few component points"}

    geom = cand.get("d21_geometry", {}) or {}
    tangent = geom.get("tangent_board")
    if tangent is None:
        center_px = cand.get("center_px", [0.0, 0.0])
        tangent = d23._pixel_axis_to_board(H, center_px, cand.get("major_axis_px", [1.0, 0.0]))
    if tangent is None:
        return {**out, "reason": "axis unavailable"}
    tangent = np.asarray(tangent, np.float32)

    best = None
    for seg in expected_seam_segments(obs):
        seg_vec = np.asarray(seg["b"], np.float32) - np.asarray(seg["a"], np.float32)
        angle_error = axis_angle_error_deg(tangent, seg_vec)
        dists = point_segment_distances(pts, seg["a"], seg["b"])
        support = float(np.count_nonzero(dists <= float(args.d24_seam_band_mm))) / float(max(1, len(dists)))
        score = support - 0.005 * angle_error
        item = {
            "name": seg["name"],
            "support_ratio": support,
            "parallel_error_deg": angle_error,
            "score": score,
            "a": [float(seg["a"][0]), float(seg["a"][1])],
            "b": [float(seg["b"][0]), float(seg["b"][1])],
        }
        if best is None or score > float(best["score"]):
            best = item

    if best is None:
        return out
    matched = bool(
        float(best["support_ratio"]) >= float(args.d24_seam_min_support_ratio)
        and float(best["parallel_error_deg"]) <= float(args.d24_seam_parallel_deg)
    )
    return {
        **best,
        "matched": matched,
        "reason": "pose-relative seam" if matched else "seam agreement insufficient",
        "length_mm": length,
        "linearity": linearity,
    }


# -----------------------------------------------------------------------------
# D24 robust heat support and final evaluation
# -----------------------------------------------------------------------------

def robust_heat_threshold(heat: Any, args) -> Dict[str, float]:
    if heat is None:
        return {"threshold": 255.0, "median": 0.0, "mad": 0.0, "sigma": 0.0}
    values = heat.heatmap[heat.inner_mask > 0].astype(np.float32)
    if values.size == 0:
        return {"threshold": 255.0, "median": 0.0, "mad": 0.0, "sigma": 0.0}
    med = float(np.median(values))
    mad = float(np.median(np.abs(values - med)))
    sigma = max(1.0, 1.4826 * mad)
    threshold = max(float(args.d24_robust_score_min), med + float(args.d24_robust_k) * sigma)
    return {"threshold": threshold, "median": med, "mad": mad, "sigma": sigma}


def candidate_robust_support(cand: Dict[str, Any], heat: Any, threshold: float) -> float:
    comp = candidate_component_mask(heat, cand)
    if comp is None:
        return 0.0
    vals = heat.heatmap[comp > 0]
    if vals.size == 0:
        return 0.0
    return float(np.count_nonzero(vals.astype(np.float32) >= float(threshold))) / float(vals.size)


def observation_quality_report(obs: Any, args) -> Dict[str, Any]:
    if obs is None or obs.mask is None or obs.pose is None:
        return {
            "good": False,
            "reason": "pose or mask missing",
            "valid_keypoints": 0,
            "mean_kpt_conf": 0.0,
        }
    confs = list(obs.pose.keypoint_conf.values())
    valid_kpts = len(confs)
    mean_conf = float(np.mean(confs)) if confs else 0.0
    checks = {
        "observation_valid": bool(obs.valid),
        "pose_valid": bool(obs.pose.valid),
        "mask_area": float(obs.mask.area_px) >= 1200.0,
        "valid_keypoints": valid_kpts >= int(args.min_valid_keypoints),
        "mean_kpt_conf": mean_conf >= float(args.min_mean_kpt_conf),
    }
    return {
        "good": bool(all(checks.values())),
        "reason": "OK" if all(checks.values()) else "observation quality low",
        "checks": checks,
        "valid_keypoints": valid_kpts,
        "mean_kpt_conf": mean_conf,
        "pose_tta_state": str(obs.pose.tta_state),
        "pose_tta_score": float(obs.pose.tta_score),
        "pose_tta_tested": int(obs.pose.tta_tested_count),
        "mask_area_px": float(obs.mask.area_px),
    }


def _d24v2_waist_reference(obs: Any, heat: Any, H: np.ndarray, robust: Dict[str, float], args) -> Dict[str, Any]:
    """Measure a visible waistband structural response as a per-garment ruler.

    D23 already removes pose-known waistband candidates from robot/finish
    candidates. D24-v2 independently samples the raw heatmap inside a narrow
    pose-relative waistband band, so small residual wrinkles can be compared
    with the garment's own natural waistband response.
    """
    out: Dict[str, Any] = {
        "valid": False,
        "reason": "waist reference unavailable",
        "length_mm": 0.0,
        "area_px": 0.0,
        "mean_response": 0.0,
        "max_response": 0.0,
        "waist_width_mm": 0.0,
        "component_count": 0,
    }
    if not bool(getattr(args, "d24v2_waist_relative_enable", True)):
        out["reason"] = "disabled"
        return out
    if obs is None or obs.pose is None or not obs.pose.valid or heat is None or H is None:
        return out

    p = obs.pose
    wl = np.asarray(p.waist_left, np.float32)
    wc = np.asarray(p.waist_center, np.float32)
    wr = np.asarray(p.waist_right, np.float32)
    lower = np.asarray(p.lower_center, np.float32)
    body_u = d23._safe_unit(lower - wc)
    waist_u = d23._safe_unit(wr - wl)
    if abs(float(np.dot(body_u, waist_u))) > 0.55:
        waist_u = np.asarray([-body_u[1], body_u[0]], np.float32)

    waist_width = max(1.0, float(np.linalg.norm(wr - wl)))
    half_width = 0.5 * waist_width + float(args.d24v2_waist_ref_side_expand_mm)
    back = max(0.0, float(args.d24v2_waist_ref_back_mm))
    forward = max(0.0, float(args.d24v2_waist_ref_forward_mm))
    corners = [
        wc - waist_u * half_width - body_u * back,
        wc + waist_u * half_width - body_u * back,
        wc + waist_u * half_width + body_u * forward,
        wc - waist_u * half_width + body_u * forward,
    ]
    band = d23._d19_board_polygon_to_mask(H, corners, heat.heatmap.shape)
    band = cv2.bitwise_and((band > 0).astype(np.uint8) * 255, (heat.inner_mask > 0).astype(np.uint8) * 255)
    out["waist_width_mm"] = waist_width
    out["band_area_px"] = int(cv2.countNonZero(band))
    if cv2.countNonZero(band) < 30:
        out["reason"] = "waist band too small"
        return out

    threshold = max(
        20.0,
        float(robust.get("threshold", 255.0)) * float(args.d24v2_waist_ref_threshold_scale),
    )
    binary = np.zeros_like(heat.heatmap, np.uint8)
    binary[(heat.heatmap.astype(np.float32) >= threshold) & (band > 0)] = 255
    binary = cv2.morphologyEx(binary, cv2.MORPH_CLOSE, np.ones((5, 5), np.uint8), iterations=1)
    binary = cv2.morphologyEx(binary, cv2.MORPH_OPEN, np.ones((3, 3), np.uint8), iterations=1)

    n, labels, stats, _ = cv2.connectedComponentsWithStats((binary > 0).astype(np.uint8), 8)
    candidates: List[Dict[str, Any]] = []
    min_area = max(1.0, float(args.d24v2_waist_ref_min_area_px))
    min_length = waist_width * float(args.d24v2_waist_ref_min_length_ratio)
    parallel_limit = float(args.d24v2_waist_ref_parallel_deg)
    for label in range(1, n):
        area = float(stats[label, cv2.CC_STAT_AREA])
        if area < min_area:
            continue
        comp = ((labels == label).astype(np.uint8) * 255)
        geom = d23._d21_component_geometry_model(comp, H, args)
        tangent = d23._safe_unit(np.asarray(geom.get("tangent_board", [1.0, 0.0]), np.float32))
        parallel_error = float(np.degrees(np.arccos(np.clip(abs(float(np.dot(tangent, waist_u))), -1.0, 1.0))))
        shape_class = str(geom.get("shape_class", ""))
        length = float(geom.get("arc_length_mm", 0.0)) if shape_class == "CURVE" else float(geom.get("major_length_mm", 0.0))
        vals = heat.heatmap[comp > 0].astype(np.float32)
        mean_response = float(np.mean(vals)) if vals.size else 0.0
        max_response = float(np.max(vals)) if vals.size else 0.0
        if parallel_error > parallel_limit or length < min_length:
            continue
        score = length * math.sqrt(max(1.0, area)) * max(0.1, mean_response / 255.0)
        candidates.append({
            "length_mm": length,
            "area_px": area,
            "mean_response": mean_response,
            "max_response": max_response,
            "parallel_error_deg": parallel_error,
            "score": score,
        })

    out["component_count"] = len(candidates)
    out["threshold"] = threshold
    if not candidates:
        out["reason"] = "no reliable parallel waistband component"
        return out
    best = max(candidates, key=lambda x: float(x["score"]))
    out.update(best)
    out["valid"] = True
    out["reason"] = "pose-relative waistband component"
    return out


def _d24v2_candidate_metrics(cand: Dict[str, Any], heat: Any, obs: Any, waist_ref: Dict[str, Any]) -> Dict[str, Any]:
    comp = candidate_component_mask(heat, cand)
    vals = heat.heatmap[comp > 0].astype(np.float32) if comp is not None else np.asarray([], np.float32)
    geom = cand.get("d21_geometry", {}) or {}
    shape_class = str(geom.get("shape_class", ""))
    length = float(geom.get("arc_length_mm", cand.get("major_length_mm", 0.0))) if shape_class == "CURVE" else float(cand.get("major_length_mm", 0.0))
    area = float(cand.get("area_px", 0.0))
    mask_area = max(1.0, float(obs.mask.area_px))
    waist_width = max(1.0, float(waist_ref.get("waist_width_mm", getattr(obs.pose, "waist_width_mm", 1.0))))
    return {
        "length_mm": length,
        "area_px": area,
        "area_ratio": area / mask_area,
        "mean_response": float(np.mean(vals)) if vals.size else float(cand.get("mean_score", 0.0)),
        "max_response": float(np.max(vals)) if vals.size else float(cand.get("max_score", 0.0)),
        "severity": float(cand.get("d21_severity", 0.0)),
        "waist_span_ratio": length / waist_width,
        "tier": int(cand.get("d20_priority_tier", 0)),
    }


def _d24v2_relative_and_major(metrics: Dict[str, Any], waist_ref: Dict[str, Any], args) -> Tuple[bool, bool, List[str]]:
    smaller_than_waist = False
    if bool(waist_ref.get("valid", False)):
        smaller_than_waist = bool(
            float(metrics["length_mm"]) < float(waist_ref["length_mm"]) * float(args.d24v2_waist_length_ratio_ignore)
            and float(metrics["area_px"]) < float(waist_ref["area_px"]) * float(args.d24v2_waist_area_ratio_ignore)
            and float(metrics["mean_response"]) < float(waist_ref["mean_response"]) * float(args.d24v2_waist_response_ratio_ignore)
        )

    reasons: List[str] = []
    if float(metrics["length_mm"]) >= float(args.d24v2_major_length_mm):
        reasons.append("long")
    if float(metrics["area_ratio"]) >= float(args.d24v2_major_area_ratio):
        reasons.append("large_area")
    if (
        float(metrics["severity"]) >= float(args.d24v2_major_severity)
        and float(metrics["length_mm"]) >= float(args.d24v2_major_severity_min_length_mm)
    ):
        reasons.append("severe")
    if (
        float(metrics["waist_span_ratio"]) >= float(args.d24v2_major_waist_span_ratio)
        and float(metrics["area_ratio"]) >= float(args.d24v2_major_waist_span_min_area_ratio)
    ):
        reasons.append("cross_span")
    major = bool(reasons)
    return smaller_than_waist, major, reasons


def evaluate_d24(obs: Any, heat: Any, H: np.ndarray, state: D24State, args) -> Dict[str, Any]:
    state.evaluation_count += 1
    quality = observation_quality_report(obs, args)

    if not quality["good"]:
        state.ready_streak = 0
        return {
            "status": "REJUDGE", "reason": "OBSERVATION_INVALID",
            "evaluation": state.evaluation_count, "quality": quality,
            "stability": {"good": False, "reason": "not appended"},
            "shape": {}, "wrinkle": {},
        }

    state.history.append(observation_entry(obs))
    stability = temporal_stability_report(state.history, args)
    if not stability["good"]:
        state.ready_streak = 0
        return {
            "status": "REJUDGE", "reason": "OBSERVATION_UNSTABLE",
            "evaluation": state.evaluation_count, "quality": quality,
            "stability": stability, "shape": {}, "wrinkle": {},
        }

    # D24-v2 hard gate 1: pants geometry/silhouette must look spread.
    shape = d23._d19_finish_shape_report(obs, args, H)
    if not bool(shape.get("shape_good", False)):
        state.ready_streak = 0
        return {
            "status": "NOT_READY_SHAPE", "reason": "PANTS_SHAPE_FAILED",
            "evaluation": state.evaluation_count, "quality": quality,
            "stability": stability, "shape": shape, "wrinkle": {},
        }

    if heat is None:
        state.ready_streak = 0
        return {
            "status": "REJUDGE", "reason": "HEATMAP_UNAVAILABLE",
            "evaluation": state.evaluation_count, "quality": quality,
            "stability": stability, "shape": shape, "wrinkle": {},
        }

    robust = robust_heat_threshold(heat, args)
    waist_ref = _d24v2_waist_reference(obs, heat, H, robust, args)
    candidates = list(getattr(heat, "d21v4_all_candidates", [])) or list(getattr(heat, "candidates", []))

    major_blockers: List[Dict[str, Any]] = []
    relative_allowed: List[Dict[str, Any]] = []
    non_major_allowed: List[Dict[str, Any]] = []
    t1: List[Dict[str, Any]] = []
    t2: List[Dict[str, Any]] = []
    seam_ignored: List[Dict[str, Any]] = []
    robust_rejected: List[Dict[str, Any]] = []

    for original in candidates:
        cand = dict(original)
        seam = seam_veto_report(cand, heat, obs, H, args)
        cand["d24_seam"] = seam
        if bool(seam.get("matched", False)):
            seam_ignored.append(cand)
            continue

        support = candidate_robust_support(cand, heat, float(robust["threshold"]))
        cand["d24_robust_support"] = support
        if support < float(args.d24_candidate_min_robust_support):
            robust_rejected.append(cand)
            continue

        metrics = _d24v2_candidate_metrics(cand, heat, obs, waist_ref)
        smaller, major, reasons = _d24v2_relative_and_major(metrics, waist_ref, args)
        cand["d24v2_metrics"] = metrics
        cand["d24v2_smaller_than_waist"] = smaller
        cand["d24v2_major"] = major
        cand["d24v2_major_reasons"] = reasons

        if major:
            major_blockers.append(cand)
        elif smaller:
            relative_allowed.append(cand)
        else:
            non_major_allowed.append(cand)

        if int(metrics["tier"]) <= 1:
            t1.append(cand)
        elif int(metrics["tier"]) == 2:
            t2.append(cand)

    # Only major blockers influence READY. Fine/T2 counts and the total heatmap
    # ratio remain visible diagnostics but never keep a well-shaped pair of pants
    # in NOT_READY forever.
    mask_area = max(1.0, float(obs.mask.area_px))
    effective_area = max(1.0, float(cv2.countNonZero(heat.inner_mask)))
    blocker_area = float(sum(float(c.get("area_px", 0.0)) for c in major_blockers))
    blocker_ratio = blocker_area / effective_area
    max_blob_ratio = max([float(c.get("area_px", 0.0)) / mask_area for c in major_blockers] or [0.0])
    max_severity = max([float((c.get("d24v2_metrics", {}) or {}).get("severity", 0.0)) for c in major_blockers] or [0.0])
    checks = {"major_wrinkle_count": len(major_blockers) <= int(args.finish_max_t3_count)}
    wrinkle_good = bool(all(checks.values()))
    wrinkle_report = {
        "policy": "SHAPE_PLUS_MAJOR_WRINKLE_ONLY",
        "good": wrinkle_good,
        "checks": checks,
        "t3_count": len(major_blockers),
        "t2_count": len(t2),
        "t1_allowed_count": len(t1),
        "relative_allowed_count": len(relative_allowed),
        "non_major_allowed_count": len(non_major_allowed),
        "seam_ignored_count": len(seam_ignored),
        "robust_rejected_count": len(robust_rejected),
        "waist_structure_ignored_count": int(getattr(heat, "d23_waist_structure_ignored_count", 0)),
        "fine_ignored_count": int(getattr(heat, "d21v4_fine_ignored_count", 0)),
        "max_severity": max_severity,
        "actionable_ratio": blocker_ratio,
        "max_blob_ratio": max_blob_ratio,
        "waist_reference": waist_ref,
        "robust": robust,
        "limits": {
            "max_major_count": int(args.finish_max_t3_count),
            "major_length_mm": float(args.d24v2_major_length_mm),
            "major_area_ratio": float(args.d24v2_major_area_ratio),
            "waist_length_ignore_ratio": float(args.d24v2_waist_length_ratio_ignore),
            "waist_area_ignore_ratio": float(args.d24v2_waist_area_ratio_ignore),
            "waist_response_ignore_ratio": float(args.d24v2_waist_response_ratio_ignore),
        },
        "remaining": [k for k, v in checks.items() if not v],
        "t1": t1,
        "t2": t2,
        "t3": major_blockers,
        "major_blockers": major_blockers,
        "relative_allowed": relative_allowed,
        "non_major_allowed": non_major_allowed,
        "seam_ignored": seam_ignored,
        "robust_rejected": robust_rejected,
    }

    if not wrinkle_good:
        state.ready_streak = 0
        return {
            "status": "NOT_READY_WRINKLE", "reason": "MAJOR_WRINKLE_REMAINS",
            "evaluation": state.evaluation_count, "quality": quality,
            "stability": stability, "shape": shape, "wrinkle": wrinkle_report,
            "ready_streak": 0, "ready_required": int(args.ready_confirm_count),
        }

    state.ready_streak += 1
    required = max(1, int(args.ready_confirm_count))
    status = "READY_GOOD_ENOUGH" if state.ready_streak >= required else "READY_PENDING"
    return {
        "status": status, "reason": "SHAPE_OK_AND_NO_MAJOR_WRINKLE",
        "evaluation": state.evaluation_count, "quality": quality,
        "stability": stability, "shape": shape, "wrinkle": wrinkle_report,
        "ready_streak": state.ready_streak, "ready_required": required,
    }


# -----------------------------------------------------------------------------
# Visualization / logging
# -----------------------------------------------------------------------------

def put_text(img: np.ndarray, text: str, xy: Tuple[int, int], color, scale=0.55, thickness=1) -> None:
    x, y = xy
    cv2.putText(img, text, (x, y), cv2.FONT_HERSHEY_SIMPLEX, scale, (0, 0, 0), thickness + 3, cv2.LINE_AA)
    cv2.putText(img, text, (x, y), cv2.FONT_HERSHEY_SIMPLEX, scale, color, thickness, cv2.LINE_AA)


def draw_candidate_box(img: np.ndarray, cand: Dict[str, Any], label: str, color) -> None:
    x, y, w, h = [int(round(float(v))) for v in cand.get("bbox", [0, 0, 0, 0])]
    cx, cy = [int(round(float(v))) for v in cand.get("center_px", [x, y])]
    cv2.rectangle(img, (x, y), (x + w, y + h), color, 2)
    cv2.circle(img, (cx, cy), 5, color, -1)
    put_text(img, label, (cx + 7, cy - 7), color, scale=0.45, thickness=1)


def draw_d24_overlay(frame: np.ndarray, obs: Any, heat: Any, report: Dict[str, Any], H: np.ndarray, cfg, args) -> np.ndarray:
    # Draw pose/mask without the old yellow candidate boxes.
    base = d23.draw_bottom_overlay(
        frame, H, obs, cfg, plan=None, wrinkle_plan=None, args=None,
        motion_busy=False, motion_name="",
    )

    # Low-alpha heatmap within the valid inner ROI.
    if heat is not None and bool(args.wrinkle_heatmap_draw):
        colored = cv2.applyColorMap(heat.heatmap, cv2.COLORMAP_JET)
        alpha = float(np.clip(args.wrinkle_heatmap_alpha, 0.0, 0.7))
        m = heat.inner_mask > 0
        blended = cv2.addWeighted(base, 1.0 - alpha, colored, alpha, 0.0)
        base[m] = blended[m]

        ignore = getattr(heat, "structure_ignore_mask", None)
        if isinstance(ignore, np.ndarray):
            contours, _ = cv2.findContours((ignore > 0).astype(np.uint8), cv2.RETR_EXTERNAL, cv2.CHAIN_APPROX_SIMPLE)
            cv2.drawContours(base, contours, -1, (150, 150, 150), 2)
        center_seam = getattr(heat, "center_rise_ignore_mask", None)
        if isinstance(center_seam, np.ndarray) and cv2.countNonZero(center_seam) > 0:
            contours, _ = cv2.findContours((center_seam > 0).astype(np.uint8), cv2.RETR_EXTERNAL, cv2.CHAIN_APPROX_SIMPLE)
            cv2.drawContours(base, contours, -1, (190, 190, 190), 2)
            ys, xs = np.where(center_seam > 0)
            if len(xs):
                put_text(base, "IGNORE CENTER RISE SEAM", (int(np.mean(xs))+8, int(np.mean(ys))), (190,190,190), 0.42, 1)

    wrinkle = report.get("wrinkle", {}) or {}
    if bool(getattr(args, "d24v5_draw_allowed_fine", False)):
        for i, cand in enumerate(wrinkle.get("t1", []), 1):
            draw_candidate_box(base, cand, f"FINE ALLOW {i}", TIER_COLORS[1])
        for i, cand in enumerate(wrinkle.get("t2", []), 1):
            draw_candidate_box(base, cand, f"WRINKLE ALLOW {i}", TIER_COLORS[2])
    for i, cand in enumerate(wrinkle.get("t3", []), 1):
        draw_candidate_box(base, cand, f"FOLD {i}", TIER_COLORS[3])
    for cand in wrinkle.get("waist_gather_ignored", []):
        draw_candidate_box(base, cand, "IGNORE WAIST GATHER", (170, 170, 170))
    for cand in wrinkle.get("seam_ignored", []):
        name = str((cand.get("d24_seam", {}) or {}).get("name", "SEAM"))
        draw_candidate_box(base, cand, f"IGNORE {name}", (160, 160, 160))

    # Shape contour color.
    shape_good = bool((report.get("shape", {}) or {}).get("shape_good", False))
    if obs is not None and obs.mask is not None:
        cv2.drawContours(base, [obs.mask.contour], -1, (0, 220, 0) if shape_good else (0, 0, 255), 3)

    status = str(report.get("status", "REJUDGE"))
    color = STATUS_COLORS.get(status, (255, 255, 255))
    cv2.rectangle(base, (10, 10), (min(base.shape[1] - 10, 850), 66), (0, 0, 0), -1)
    put_text(base, status, (25, 48), color, scale=1.0, thickness=2)

    return append_status_panel(base, report, args)


def bool_mark(v: Any) -> str:
    return "PASS" if bool(v) else "FAIL"


def append_status_panel(image: np.ndarray, report: Dict[str, Any], args) -> np.ndarray:
    h = max(image.shape[0], 760)
    panel_w = max(520, int(args.panel_width))
    panel = np.zeros((h, panel_w, 3), np.uint8)
    panel[:] = (24, 24, 24)
    y = 34

    def line(text: str, color=(230, 230, 230), scale=0.47, gap=24) -> None:
        nonlocal y
        put_text(panel, text[:100], (18, y), color, scale=scale, thickness=1)
        y += gap

    status = str(report.get("status", "REJUDGE"))
    line(f"D24 FINISH: {status}", STATUS_COLORS.get(status, (255, 255, 255)), 0.72, 34)
    line(f"reason: {report.get('reason', '')}", (210, 210, 210), 0.47, 28)

    quality = report.get("quality", {}) or {}
    line("[1] OBSERVATION", (255, 220, 120), 0.52, 25)
    line(f"quality {bool_mark(quality.get('good'))}  kpts={quality.get('valid_keypoints', 0)}  meanConf={float(quality.get('mean_kpt_conf', 0.0)):.2f}")
    line(f"TTA={quality.get('pose_tta_state', '-')} score={float(quality.get('pose_tta_score', 0.0)):.1f} tested={quality.get('pose_tta_tested', 0)}")

    stability = report.get("stability", {}) or {}
    line("[2] TEMPORAL STABILITY", (255, 220, 120), 0.52, 25)
    line(f"stable {bool_mark(stability.get('good'))} history={stability.get('history_count', 0)}/{stability.get('required', args.history_count)}")
    line(f"areaDelta={float(stability.get('mask_area_rel', 0.0)):.3f}  center={float(stability.get('center_shift_mm', 0.0)):.1f}mm")
    line(f"axisSpread={float(stability.get('pose_axis_spread_deg', 0.0)):.1f}deg")

    shape = report.get("shape", {}) or {}
    sym = shape.get("symmetry", {}) or {}
    hard = shape.get("hard_checks", {}) or {}
    line("[3] PANTS SHAPE", (255, 220, 120), 0.52, 25)
    line(f"shape {bool_mark(shape.get('shape_good'))} score={float(shape.get('shape_score', 0.0)):.2f}")
    line(f"hemGap={float(shape.get('hem_gap_ratio', 0.0)):.2f}  legBalance={float(shape.get('leg_balance', 0.0)):.2f}")
    line(f"crotchAxis={float(shape.get('crotch_axis_offset_ratio', 0.0)):.2f}  bodyAxis={float(shape.get('axis_to_waist_ratio', 0.0)):.2f}")
    line(f"lowerIoU={float(sym.get('lower_reflected_iou', 0.0)):.2f}  widthMed={float(sym.get('lower_width_balance_median', 0.0)):.2f}")
    line(f"widthMin={float(sym.get('lower_width_balance_min', 0.0)):.2f}  symmetry={float(sym.get('symmetry_score', 0.0)):.2f}")
    if shape.get("remaining"):
        line("fail: " + ", ".join(str(x) for x in shape.get("remaining", [])), (80, 120, 255), 0.43, 23)

    wrinkle = report.get("wrinkle", {}) or {}
    line("[4] SHAPE + FOLD ONLY", (255, 220, 120), 0.52, 25)
    line(f"foldGate {bool_mark(wrinkle.get('good'))}  FOLD={wrinkle.get('fold_count', wrinkle.get('t3_count', 0))}  fineAllowed={wrinkle.get('fine_allowed_count', 0)}")
    line(f"waistGatherIgnored={wrinkle.get('waist_gather_ignored_count', 0)}  seamIgnored={wrinkle.get('seam_ignored_count', 0)}")
    line(f"centerRiseIgnoredPx={wrinkle.get('center_rise_ignored_px', 0)}  brightTextureLargeArea=diagnosticOnly", (190,190,190), 0.40, 23)
    line(f"foldRatio={float(wrinkle.get('actionable_ratio', 0.0)):.3f}  maxFoldBlob={float(wrinkle.get('max_blob_ratio', 0.0)):.3f}")
    line(f"waistBandVeto={wrinkle.get('waist_structure_ignored_count', 0)}  robustReject={wrinkle.get('robust_rejected_count', 0)}")
    waist_ref = wrinkle.get("waist_reference", {}) or {}
    line(f"waistRef={bool_mark(waist_ref.get('valid'))} len={float(waist_ref.get('length_mm',0.0)):.1f}mm area={float(waist_ref.get('area_px',0.0)):.0f}px")
    line(f"waistResp={float(waist_ref.get('mean_response',0.0)):.1f} reason={str(waist_ref.get('reason',''))[:36]}", (190,190,190), 0.40, 23)
    robust = wrinkle.get("robust", {}) or {}
    line(f"robustThr={float(robust.get('threshold', 0.0)):.1f} med={float(robust.get('median', 0.0)):.1f} sigma={float(robust.get('sigma', 0.0)):.1f}")
    if wrinkle.get("remaining"):
        line("fail: " + ", ".join(str(x) for x in wrinkle.get("remaining", [])), (80, 120, 255), 0.43, 23)

    line("[5] CONFIRMATION", (255, 220, 120), 0.52, 25)
    line(f"READY streak={report.get('ready_streak', 0)}/{report.get('ready_required', args.ready_confirm_count)}")
    line("Keys: SPACE evaluate | C reset | S save | L lock H | R reset H | Q quit", (180, 180, 180), 0.39, 24)

    canvas = np.zeros((h, image.shape[1] + panel_w, 3), np.uint8)
    canvas[:image.shape[0], :image.shape[1]] = image
    canvas[:, image.shape[1]:] = panel
    return canvas


def json_safe(value: Any) -> Any:
    if isinstance(value, np.ndarray):
        return value.tolist()
    if isinstance(value, (np.floating, np.integer)):
        return value.item()
    if isinstance(value, dict):
        return {str(k): json_safe(v) for k, v in value.items() if k not in {"t1", "t2", "t3", "major_blockers", "fold_blockers", "waist_gather_ignored", "fine_allowed", "relative_allowed", "non_major_allowed", "seam_ignored", "robust_rejected"}}
    if isinstance(value, (list, tuple)):
        return [json_safe(v) for v in value]
    return value


def append_jsonl(path: str, report: Dict[str, Any]) -> None:
    if not path:
        return
    record = {
        "timestamp": time.strftime("%Y-%m-%d %H:%M:%S"),
        "unix_time": time.time(),
        **json_safe(report),
    }
    try:
        with open(path, "a", encoding="utf-8") as f:
            f.write(json.dumps(record, ensure_ascii=False) + "\n")
    except Exception as exc:
        print(f"[D25-LOG-WARN] {exc!r}")


def save_sample(state: D24State, args) -> None:
    if state.latest_overlay is None:
        print("[D25-SAVE] no overlay yet")
        return
    out_dir = Path(args.snapshot_dir)
    out_dir.mkdir(parents=True, exist_ok=True)
    ts = time.strftime("%Y%m%d_%H%M%S")
    stem = f"d24_{ts}_{state.latest_status}"
    image_path = out_dir / f"{stem}.jpg"
    json_path = out_dir / f"{stem}.json"
    cv2.imwrite(str(image_path), state.latest_overlay)
    with open(json_path, "w", encoding="utf-8") as f:
        json.dump(json_safe(state.latest_report), f, ensure_ascii=False, indent=2)
    print(f"[D25-SAVE] image={image_path} report={json_path}")


# -----------------------------------------------------------------------------
# Evaluation worker / main loop
# -----------------------------------------------------------------------------

def median_frame(frames: Sequence[np.ndarray]) -> np.ndarray:
    if len(frames) == 1:
        return frames[0].copy()
    stack = np.stack(frames, axis=0).astype(np.float32)
    return np.median(stack, axis=0).astype(np.uint8)


def make_cfg(config: Dict[str, Any]) -> Any:
    cfg = d23.BottomSafetyConfig()
    xmin, xmax, ymin, ymax = d23.board_bounds_from_config(config)
    cfg.board_x_min = xmin
    cfg.board_x_max = xmax
    cfg.board_y_min = ymin
    cfg.board_y_max = ymax
    cfg.split_board_x = float(config.get("dual_roarm", {}).get("split_board_x", 247.0))
    return cfg


def evaluate_frame(frame: np.ndarray, H: np.ndarray, seg_model, pose_model, state: D24State, args, cfg) -> Tuple[Any, Any, Dict[str, Any], np.ndarray]:
    obs = d23.infer_bottom_observation(seg_model, pose_model, frame, H, args, cfg)
    heat = None
    if obs is not None and obs.mask is not None:
        heat = d23.build_d21_wrinkle_heatmap(frame, obs, H, args)
    report = evaluate_d24(obs, heat, H, state, args)
    overlay = draw_d24_overlay(frame, obs, heat, report, H, cfg, args)
    return obs, heat, report, overlay


def print_report(report: Dict[str, Any]) -> None:
    status = report.get("status", "REJUDGE")
    q = report.get("quality", {}) or {}
    st = report.get("stability", {}) or {}
    sh = report.get("shape", {}) or {}
    sy = sh.get("symmetry", {}) or {}
    wr = report.get("wrinkle", {}) or {}
    print(
        f"[D25] status={status} reason={report.get('reason')} "
        f"kpts={q.get('valid_keypoints',0)} conf={float(q.get('mean_kpt_conf',0.0)):.2f} "
        f"stable={st.get('good',False)} areaDelta={float(st.get('mask_area_rel',0.0)):.3f} "
        f"centerShift={float(st.get('center_shift_mm',0.0)):.1f}mm "
        f"shape={float(sh.get('shape_score',0.0)):.2f} "
        f"lowerIoU={float(sy.get('lower_reflected_iou',0.0)):.2f} "
        f"widthMin={float(sy.get('lower_width_balance_min',0.0)):.2f} "
        f"MAJOR={wr.get('t3_count',0)} T2shown={wr.get('t2_count',0)} waistAllowed={wr.get('relative_allowed_count',0)} "
        f"majorRatio={float(wr.get('actionable_ratio',0.0)):.3f} maxMajorBlob={float(wr.get('max_blob_ratio',0.0)):.3f} "
        f"ready={report.get('ready_streak',0)}/{report.get('ready_required','-')}"
    )


def detect_homography(frame: np.ndarray, detector, marker_board_mm, required_ids) -> Tuple[Optional[np.ndarray], Dict[int, np.ndarray]]:
    corners, ids, _ = d23.detect_markers(frame, detector)
    return d23.compute_homography(corners, ids, marker_board_mm, required_ids)


def run_single_image(args, config, cfg, H, seg_model, pose_model) -> int:
    frame = cv2.imread(args.image)
    if frame is None:
        print(f"[D25-ERROR] cannot read image: {args.image}")
        return 2
    if H is None:
        print("[D25-ERROR] Homography is required for --image. Load --hfile first.")
        return 2
    state = D24State(history=collections.deque(maxlen=max(2, int(args.history_count))))
    # Repeat the same image only for deterministic offline inspection. Mark the
    # report as one-shot; live temporal stability should be tested with a camera.
    for _ in range(max(2, int(args.history_count))):
        obs, heat, report, overlay = evaluate_frame(frame, H, seg_model, pose_model, state, args, cfg)
    state.latest_overlay = overlay
    state.latest_report = report
    state.latest_status = str(report.get("status", "REJUDGE"))
    cv2.imwrite(args.output, overlay)
    print_report(report)
    print(f"[D25] saved: {args.output}")
    return 0


def main() -> int:
    args = finalize_args(build_parser().parse_args())
    print(f"[BUILD] {STEP_D24_BUILD}")
    print("[D25-SAFETY] perception-only: no serial port, no robot command, no low-Z motion")
    print(
        f"[D25-SHAPE] score>={args.finish_shape_score_min:.2f} "
        f"hemGap={args.finish_hem_gap_ratio_min:.2f}~{args.finish_hem_gap_ratio_max:.2f} "
        f"legBalance>={args.finish_leg_balance_min:.2f} lowerIoU>={args.d22_lower_reflected_iou_min:.2f}"
    )
    print(
        f"[D24V6-FINISH] only broad contrast-supported folds block READY: count<={args.finish_max_t3_count} "
        f"length>={args.d24v2_major_length_mm:.0f}mm OR areaRatio>={args.d24v2_major_area_ratio:.3f}; "
        f"waist-relative ignore len<{args.d24v2_waist_length_ratio_ignore:.2f} area<{args.d24v2_waist_area_ratio_ignore:.2f} response<{args.d24v2_waist_response_ratio_ignore:.2f}"
    )
    print(
        f"[D24V6-STRUCTURE] waistband/crotch + radial waist-gather ignore; conditionalSeam={args.d24_seam_veto} "
        f"seamSupport>={args.d24_seam_min_support_ratio:.2f}"
    )

    config = d23.load_json_if_exists(args.config) or {
        "aruco": {
            "dictionary": "DICT_4X4_50",
            "required_ids": [0, 1, 2, 3],
            "marker_board_mm": d23.DEFAULT_MARKER_BOARD_MM,
        },
        "dual_roarm": {"split_board_x": 247.0},
    }
    cfg = make_cfg(config)
    H = d23.load_homography(args.hfile) if args.load_h else None
    if H is not None:
        print(f"[H] loaded: {args.hfile}")

    seg_model, pose_model = d23.load_models(args)

    if args.image:
        return run_single_image(args, config, cfg, H, seg_model, pose_model)

    detector = d23.make_aruco_detector(
        d23.get_dictionary(config.get("aruco", {}).get("dictionary", "DICT_4X4_50"))
    )
    required_ids = config.get("aruco", {}).get("required_ids", [0, 1, 2, 3])
    marker_board_mm = config.get("aruco", {}).get("marker_board_mm", d23.DEFAULT_MARKER_BOARD_MM)

    cap = d23.open_camera(args)
    d23.configure_usb_camera(args)
    for _ in range(max(0, int(args.warmup_frames))):
        cap.read()
        time.sleep(0.02)

    frame_buffer: Deque[np.ndarray] = collections.deque(maxlen=max(1, int(args.burst_frame_count)))
    state = D24State(history=collections.deque(maxlen=max(2, int(args.history_count))))
    state.latest_h = H
    state_lock = threading.RLock()
    worker_lock = threading.Lock()
    stop_event = threading.Event()
    last_schedule = 0.0

    def worker(frames: List[np.ndarray], H_snapshot: np.ndarray) -> None:
        nonlocal last_schedule
        try:
            med = median_frame(frames)
            with state_lock:
                state.last_eval_started = time.time()
            obs, heat, report, overlay = evaluate_frame(
                med, H_snapshot, seg_model, pose_model, state, args, cfg
            )
            with state_lock:
                state.latest_obs = obs
                state.latest_heat = heat
                state.latest_report = report
                state.latest_status = str(report.get("status", "REJUDGE"))
                state.latest_overlay = overlay
                state.latest_eval_frame = med
                state.latest_h = H_snapshot.copy()
            print_report(report)
            append_jsonl(args.log_jsonl, report)
        except Exception as exc:
            print(f"[D25-WORKER-ERROR] {exc!r}")
            with state_lock:
                state.ready_streak = 0
                state.latest_status = "REJUDGE"
                state.latest_report = {
                    "status": "REJUDGE",
                    "reason": f"worker error: {exc!r}",
                }
        finally:
            worker_lock.release()

    try:
        while not stop_event.is_set():
            ok, frame = cap.read()
            if not ok or frame is None:
                time.sleep(0.03)
                continue
            frame_buffer.append(frame.copy())

            H_candidate, marker_centers = detect_homography(frame, detector, marker_board_mm, required_ids)
            if H is None and bool(args.auto_lock) and H_candidate is not None:
                H = H_candidate
                with state_lock:
                    state.latest_h = H.copy()
                if bool(args.save_h_on_lock):
                    d23.save_homography(args.hfile, H)
                print("[H] auto-locked from ArUco markers")

            now = time.time()
            with state_lock:
                force = bool(state.force_evaluate)
                state.force_evaluate = False
                paused = bool(state.paused)
            due = force or (now - last_schedule >= max(0.20, float(args.eval_interval_s)))
            if (
                not paused and due and H is not None
                and len(frame_buffer) >= max(1, int(args.burst_frame_count))
                and worker_lock.acquire(blocking=False)
            ):
                last_schedule = now
                frames = [f.copy() for f in frame_buffer]
                threading.Thread(target=worker, args=(frames, H.copy()), daemon=True).start()

            with state_lock:
                shown = state.latest_overlay.copy() if state.latest_overlay is not None else frame.copy()
                latest_report = dict(state.latest_report)

            if state.latest_overlay is None:
                status = "WAITING FOR FIRST EVALUATION" if H is not None else "LOCK HOMOGRAPHY: show IDs 0,1,2,3"
                put_text(shown, status, (25, 45), (0, 220, 255), scale=0.75, thickness=2)

            if not args.no_window:
                cv2.imshow(args.window_name, shown)
                key = cv2.waitKey(1) & 0xFF
            else:
                key = 255

            terminal_key = d23.read_terminal_key()
            if terminal_key != 255:
                key = terminal_key

            if key in (27, ord("q"), ord("Q")):
                break
            if key == ord(" "):
                with state_lock:
                    state.force_evaluate = True
            elif key in (ord("c"), ord("C")):
                with state_lock:
                    state.reset_temporal()
                print("[D25] temporal history and READY streak cleared")
            elif key in (ord("s"), ord("S")):
                with state_lock:
                    save_sample(state, args)
            elif key in (ord("p"), ord("P")):
                with state_lock:
                    state.paused = not state.paused
                    print(f"[D25] paused={state.paused}")
            elif key in (ord("l"), ord("L")):
                if H_candidate is None:
                    print(f"[H] lock failed; visible marker IDs={sorted(marker_centers.keys())}")
                else:
                    H = H_candidate
                    with state_lock:
                        state.latest_h = H.copy()
                        state.reset_temporal()
                    if bool(args.save_h_on_lock):
                        d23.save_homography(args.hfile, H)
                    print("[H] locked/updated")
            elif key in (ord("r"), ord("R")):
                H = None
                with state_lock:
                    state.latest_h = None
                    state.reset_temporal()
                print("[H] reset in memory")

            if args.once and state.evaluation_count >= max(2, int(args.history_count)):
                # Save the most recent state after enough history exists.
                with state_lock:
                    if state.latest_overlay is not None:
                        cv2.imwrite(args.output, state.latest_overlay)
                        print(f"[D25] once overlay saved: {args.output}")
                break

    finally:
        stop_event.set()
        cap.release()
        if not args.no_window:
            cv2.destroyAllWindows()

    return 0




# =============================================================================
# D24-v3: A119 heatmap transplant + frozen snapshot evaluation
# =============================================================================

@dataclass
class A119BottomHeatmapPlan:
    """A119-style heatmap container compatible with D24-v2 visualization helpers."""
    heatmap: np.ndarray
    inner_mask: np.ndarray
    binary: np.ndarray
    candidates: List[Dict[str, Any]]
    threshold: float
    wrinkle_ratio: float
    status: str
    summary: str
    ready_heatmap: np.ndarray
    ready_inner_mask: np.ndarray
    ready_threshold: float
    ready_roi_valid: bool
    d21v4_all_candidates: List[Dict[str, Any]] = field(default_factory=list)
    d21v4_residual_binary: Optional[np.ndarray] = None
    structure_ignore_mask: Optional[np.ndarray] = None
    structure_info: Dict[str, Any] = field(default_factory=dict)
    d23_waist_structure_ignored_count: int = 0
    d21v4_fine_ignored_count: int = 0
    highpass_abs: Optional[np.ndarray] = None
    center_rise_ignore_mask: Optional[np.ndarray] = None
    center_rise_info: Dict[str, Any] = field(default_factory=dict)


def _a119_odd_ksize(value: int, minimum: int = 3) -> int:
    k = max(int(minimum), int(value))
    return k if k % 2 == 1 else k + 1


def _a119_normalize_u8(arr: np.ndarray, mask: Optional[np.ndarray]) -> np.ndarray:
    """A119 2~98 percentile normalization inside the selected garment ROI."""
    a = np.asarray(arr, dtype=np.float32)
    out = np.zeros(a.shape, dtype=np.uint8)
    if mask is None:
        valid = np.isfinite(a)
    else:
        valid = (np.asarray(mask) > 0) & np.isfinite(a)
    if not np.any(valid):
        return out
    vals = a[valid]
    lo = float(np.percentile(vals, 2.0))
    hi = float(np.percentile(vals, 98.0))
    if hi <= lo + 1e-6:
        return out
    scaled = np.clip((a - lo) * (255.0 / (hi - lo)), 0.0, 255.0).astype(np.uint8)
    scaled[~valid] = 0
    return scaled


def _a119_px_per_mm(H: np.ndarray, center_board: Sequence[float]) -> Optional[float]:
    try:
        c = np.asarray(center_board, dtype=np.float32).reshape(2)
        p0 = d23.board_to_pixel(H, float(c[0]), float(c[1]))
        p1 = d23.board_to_pixel(H, float(c[0] + 50.0), float(c[1]))
        p2 = d23.board_to_pixel(H, float(c[0]), float(c[1] + 50.0))
        scales: List[float] = []
        if p0 is not None and p1 is not None:
            scales.append(float(np.linalg.norm(np.asarray(p1) - np.asarray(p0))) / 50.0)
        if p0 is not None and p2 is not None:
            scales.append(float(np.linalg.norm(np.asarray(p2) - np.asarray(p0))) / 50.0)
        return float(np.median(scales)) if scales else None
    except Exception:
        return None


def _a119_inner_roi(mask_u8: np.ndarray, px_per_mm: Optional[float], margin_mm: float,
                    min_keep_ratio: float = 0.10) -> Tuple[np.ndarray, float]:
    mask = ((np.asarray(mask_u8) > 0).astype(np.uint8) * 255)
    if margin_mm <= 0.0 or px_per_mm is None or px_per_mm <= 1e-6:
        return mask, 0.0
    dist = cv2.distanceTransform((mask > 0).astype(np.uint8), cv2.DIST_L2, 5)
    base = int(cv2.countNonZero(mask))
    min_keep = max(200, int(base * float(np.clip(min_keep_ratio, 0.02, 0.95))))
    for factor in (1.0, 0.80, 0.60, 0.45):
        margin_px = max(1, int(round(float(margin_mm) * factor * float(px_per_mm))))
        roi = (((dist >= float(margin_px)) & (mask > 0)).astype(np.uint8) * 255)
        if int(cv2.countNonZero(roi)) >= min_keep:
            return roi, float(margin_mm) * factor
    return mask, 0.0


def _a119_component_geometry(component: np.ndarray, H: np.ndarray) -> Dict[str, Any]:
    ys, xs = np.where(component > 0)
    if len(xs) < 5:
        return {
            "center_px": [0.0, 0.0], "major_axis_px": [1.0, 0.0],
            "minor_axis_px": [0.0, 1.0], "major_length_px": 0.0,
            "minor_length_px": 1.0, "major_length_mm": 0.0,
            "minor_length_mm": 1.0, "linearity": 1.0,
            "tangent_board": [1.0, 0.0], "normal_board": [0.0, 1.0],
        }
    pts_px = np.column_stack([xs, ys]).astype(np.float32)
    center_px = pts_px.mean(axis=0)
    centered_px = pts_px - center_px.reshape(1, 2)
    try:
        vals, vecs = np.linalg.eigh(np.cov(centered_px.T))
        major_axis_px = vecs[:, int(np.argmax(vals))].astype(np.float32)
        major_axis_px /= max(1e-6, float(np.linalg.norm(major_axis_px)))
    except Exception:
        major_axis_px = np.asarray([1.0, 0.0], np.float32)
    minor_axis_px = np.asarray([-major_axis_px[1], major_axis_px[0]], np.float32)
    pmaj_px = centered_px @ major_axis_px
    pmin_px = centered_px @ minor_axis_px
    major_len_px = float(np.ptp(pmaj_px)) if pmaj_px.size else 0.0
    minor_len_px = float(np.ptp(pmin_px)) if pmin_px.size else 1.0

    sample = pts_px
    if len(sample) > 2500:
        sample = sample[::max(1, int(math.ceil(len(sample) / 2500.0)))]
    try:
        pts_board = cv2.perspectiveTransform(sample.reshape(-1, 1, 2), H).reshape(-1, 2)
        center_board = pts_board.mean(axis=0)
        centered_board = pts_board - center_board.reshape(1, 2)
        vals_b, vecs_b = np.linalg.eigh(np.cov(centered_board.T))
        tangent = vecs_b[:, int(np.argmax(vals_b))].astype(np.float32)
        tangent /= max(1e-6, float(np.linalg.norm(tangent)))
        normal = np.asarray([-tangent[1], tangent[0]], np.float32)
        pmaj = centered_board @ tangent
        pmin = centered_board @ normal
        major_len_mm = float(np.ptp(pmaj)) if pmaj.size else 0.0
        minor_len_mm = float(np.ptp(pmin)) if pmin.size else 1.0
    except Exception:
        center_board = np.asarray([0.0, 0.0], np.float32)
        tangent = np.asarray([1.0, 0.0], np.float32)
        normal = np.asarray([0.0, 1.0], np.float32)
        major_len_mm = 0.0
        minor_len_mm = 1.0

    return {
        "center_px": [float(center_px[0]), float(center_px[1])],
        "center_board": [float(center_board[0]), float(center_board[1])],
        "major_axis_px": [float(major_axis_px[0]), float(major_axis_px[1])],
        "minor_axis_px": [float(minor_axis_px[0]), float(minor_axis_px[1])],
        "major_length_px": major_len_px,
        "minor_length_px": minor_len_px,
        "major_length_mm": major_len_mm,
        "minor_length_mm": minor_len_mm,
        "linearity": float(major_len_mm / max(1.0, minor_len_mm)),
        "tangent_board": [float(tangent[0]), float(tangent[1])],
        "normal_board": [float(normal[0]), float(normal[1])],
    }


def _d24v6_center_rise_structure_mask(obs: Any, H: np.ndarray, image_shape, args) -> Tuple[np.ndarray, Dict[str, Any]]:
    """Return a narrow pose-relative center-rise seam mask.

    The mask follows waist_center -> crotch in board coordinates, so it is
    independent of the pants rotation in the camera image. Only a narrow strip
    is erased; a genuinely broad fold crossing the seam remains as residual
    components on one or both sides after CCA is rebuilt.
    """
    out = np.zeros(image_shape[:2], dtype=np.uint8)
    info: Dict[str, Any] = {"valid": False, "ignored_px": 0, "reason": "disabled"}
    if not bool(getattr(args, "d24v6_center_rise_ignore", True)):
        return out, info
    if obs is None or obs.pose is None or not obs.pose.valid or H is None:
        info["reason"] = "pose invalid"
        return out, info
    wc = np.asarray(obs.pose.waist_center, np.float32).reshape(2)
    cr = np.asarray(obs.pose.crotch, np.float32).reshape(2)
    axis = cr - wc
    length = float(np.linalg.norm(axis))
    if length < 25.0:
        info["reason"] = "waist-crotch axis too short"
        return out, info
    u = axis / length
    n = np.asarray([-u[1], u[0]], np.float32)
    start_mm = float(np.clip(float(getattr(args, "d24v6_center_rise_start_mm", 48.0)), 0.0, max(0.0, length - 5.0)))
    end_before = max(0.0, float(getattr(args, "d24v6_center_rise_end_before_crotch_mm", 0.0)))
    end_expand = max(0.0, float(getattr(args, "d24v6_center_rise_end_expand_mm", 12.0)))
    half_w = max(4.0, float(getattr(args, "d24v6_center_rise_half_width_mm", 18.0)))
    start = wc + u * start_mm
    end = cr - u * end_before + u * end_expand
    poly = [start - n * half_w, start + n * half_w, end + n * half_w, end - n * half_w]
    out = d23._d19_board_polygon_to_mask(H, poly, image_shape)
    if obs.mask is not None and obs.mask.mask_u8.shape[:2] == out.shape[:2]:
        out = cv2.bitwise_and(out, obs.mask.mask_u8)
    info.update({
        "valid": True,
        "reason": "pose-relative center-rise seam",
        "ignored_px": int(cv2.countNonZero(out)),
        "axis_length_mm": length,
        "start_mm": start_mm,
        "half_width_mm": half_w,
        "start_board": [float(start[0]), float(start[1])],
        "end_board": [float(end[0]), float(end[1])],
    })
    return out, info


def _d24v6_component_contrast(cand: Dict[str, Any], heat: Any, args) -> Dict[str, float]:
    """Measure original-scale local contrast rather than normalized heat only."""
    comp = candidate_component_mask(heat, cand)
    hp = getattr(heat, "highpass_abs", None)
    if comp is None or not isinstance(hp, np.ndarray) or hp.shape[:2] != comp.shape[:2]:
        return {"mean_abs_contrast": 0.0, "contrast_support": 0.0}
    vals = hp[comp > 0].astype(np.float32)
    if vals.size == 0:
        return {"mean_abs_contrast": 0.0, "contrast_support": 0.0}
    pix_thr = float(getattr(args, "d24v6_fold_contrast_pixel_threshold", 8.0))
    return {
        "mean_abs_contrast": float(np.mean(vals)),
        "contrast_support": float(np.count_nonzero(vals >= pix_thr)) / float(vals.size),
    }


def build_a119_bottom_heatmap(frame: np.ndarray, obs: Any, H: np.ndarray, args) -> Optional[A119BottomHeatmapPlan]:
    """Transplant A119's heatmap and READY CCA front-end to bottom garments.

    A119 channels:
      30% high-pass shading + 30% Sobel magnitude + 20% Laplacian
      + 20% max response from four Gabor orientations.

    D24-v3 then applies the bottom-specific pose structure mask before connected
    component analysis. The raw heatmap remains available for waistband-relative
    comparison, while candidates are generated only from the cleaned binary.
    """
    if frame is None or obs is None or obs.mask is None or H is None:
        return None
    mask_u8 = ((obs.mask.mask_u8 > 0).astype(np.uint8) * 255)
    if cv2.countNonZero(mask_u8) < 200:
        return None

    gray = cv2.cvtColor(frame, cv2.COLOR_BGR2GRAY) if frame.ndim == 3 else frame.copy()
    clahe = cv2.createCLAHE(
        clipLimit=max(0.1, float(args.wrinkle_heatmap_clahe_clip)),
        tileGridSize=(max(2, int(args.wrinkle_heatmap_clahe_tile)),) * 2,
    )
    eq = clahe.apply(gray)
    blur_k = _a119_odd_ksize(int(args.wrinkle_heatmap_blur_ksize), 7)
    illum = cv2.GaussianBlur(eq, (blur_k, blur_k), 0)
    high = cv2.absdiff(eq, illum).astype(np.float32)
    sx = cv2.Sobel(eq, cv2.CV_32F, 1, 0, ksize=3)
    sy = cv2.Sobel(eq, cv2.CV_32F, 0, 1, ksize=3)
    grad = cv2.magnitude(sx, sy)
    lap = np.abs(cv2.Laplacian(eq, cv2.CV_32F, ksize=3))

    gabor_resp = np.zeros_like(grad, dtype=np.float32)
    if bool(args.wrinkle_heatmap_gabor):
        gk = _a119_odd_ksize(int(args.wrinkle_heatmap_gabor_ksize), 7)
        sigma = max(0.5, float(args.wrinkle_heatmap_gabor_sigma))
        lambd = max(2.0, float(args.wrinkle_heatmap_gabor_lambda))
        for theta in (0.0, np.pi / 4.0, np.pi / 2.0, 3.0 * np.pi / 4.0):
            kernel = cv2.getGaborKernel((gk, gk), sigma, theta, lambd, gamma=0.45, psi=0, ktype=cv2.CV_32F)
            resp = cv2.filter2D(eq, cv2.CV_32F, kernel)
            gabor_resp = np.maximum(gabor_resp, np.abs(resp))

    center_board = np.asarray(obs.mask.center_board, np.float32).reshape(2)
    px_per_mm = _a119_px_per_mm(H, center_board)
    # A119 READY branch uses a wider 15 mm inner region than its 30 mm action ROI.
    ready_margin_mm = 15.0
    inner_mask, used_margin_mm = _a119_inner_roi(mask_u8, px_per_mm, ready_margin_mm, 0.10)

    high_n = _a119_normalize_u8(high, inner_mask)
    grad_n = _a119_normalize_u8(grad, inner_mask)
    lap_n = _a119_normalize_u8(lap, inner_mask)
    gabor_n = _a119_normalize_u8(gabor_resp, inner_mask) if bool(args.wrinkle_heatmap_gabor) else np.zeros_like(high_n)
    combined = (
        0.30 * high_n.astype(np.float32)
        + 0.30 * grad_n.astype(np.float32)
        + 0.20 * lap_n.astype(np.float32)
        + 0.20 * gabor_n.astype(np.float32)
    )
    heat = _a119_normalize_u8(combined, inner_mask)
    heat[inner_mask <= 0] = 0
    vals = heat[inner_mask > 0]
    if vals.size == 0:
        return None
    threshold = max(
        float(args.wrinkle_heatmap_score_min),
        float(np.percentile(vals, np.clip(float(args.wrinkle_heatmap_percentile), 50.0, 99.5))),
    )

    # A119 READY-only spatial median + opening + dilation.
    heat_ready = cv2.medianBlur(heat, 3)
    heat_ready[inner_mask <= 0] = 0
    binary_pre = np.zeros_like(heat_ready, np.uint8)
    binary_pre[(heat_ready >= threshold) & (inner_mask > 0)] = 255
    binary_pre = cv2.morphologyEx(
        binary_pre, cv2.MORPH_OPEN,
        cv2.getStructuringElement(cv2.MORPH_ELLIPSE, (3, 3)), iterations=1,
    )
    binary_pre = cv2.dilate(
        binary_pre, cv2.getStructuringElement(cv2.MORPH_ELLIPSE, (3, 3)), iterations=1,
    )

    # Bottom-specific static structure removal: waistband + crotch. Side/inner/hem
    # seams are still conditionally vetoed later using pose-relative line agreement.
    structure_mask, structure_info = d23._d19_pose_ignore_mask(obs, H, args)
    if structure_mask.shape != binary_pre.shape:
        structure_mask = cv2.resize(structure_mask, (binary_pre.shape[1], binary_pre.shape[0]), interpolation=cv2.INTER_NEAREST)
    center_rise_mask, center_rise_info = _d24v6_center_rise_structure_mask(obs, H, binary_pre.shape, args)
    if center_rise_mask.shape != binary_pre.shape:
        center_rise_mask = cv2.resize(center_rise_mask, (binary_pre.shape[1], binary_pre.shape[0]), interpolation=cv2.INTER_NEAREST)
    structure_mask = cv2.bitwise_or(structure_mask, center_rise_mask)
    structure_info = dict(structure_info or {})
    structure_info["center_rise"] = center_rise_info
    structure_info["center_rise_px"] = int(cv2.countNonZero(center_rise_mask))
    structure_info["ignored_px"] = int(cv2.countNonZero(structure_mask))
    cleaned_binary = binary_pre.copy()
    # D24-v6: structure pixels are removed first; CCA below is rebuilt only on residuals.
    cleaned_binary[structure_mask > 0] = 0

    n, labels, stats, centers = cv2.connectedComponentsWithStats((cleaned_binary > 0).astype(np.uint8), 8)
    min_blob = max(1.0, float(args.wrinkle_heatmap_min_blob_area))
    mask_area = max(1.0, float(obs.mask.area_px))
    candidates: List[Dict[str, Any]] = []
    kept = np.zeros_like(cleaned_binary)
    for label in range(1, n):
        area = float(stats[label, cv2.CC_STAT_AREA])
        if area < min_blob:
            continue
        component = ((labels == label).astype(np.uint8) * 255)
        contours, _ = cv2.findContours(component, cv2.RETR_EXTERNAL, cv2.CHAIN_APPROX_SIMPLE)
        if not contours:
            continue
        contour = max(contours, key=cv2.contourArea)
        geom = _a119_component_geometry(component, H)
        x = int(stats[label, cv2.CC_STAT_LEFT])
        y = int(stats[label, cv2.CC_STAT_TOP])
        w = int(stats[label, cv2.CC_STAT_WIDTH])
        h = int(stats[label, cv2.CC_STAT_HEIGHT])
        cx, cy = map(float, centers[label])
        component_vals = heat_ready[component > 0].astype(np.float32)
        mean_score = float(np.mean(component_vals)) if component_vals.size else 0.0
        max_score = float(np.max(component_vals)) if component_vals.size else 0.0
        length_mm = float(geom["major_length_mm"])
        aspect = float(geom["linearity"])
        strong = bool(area >= 120.0 and length_mm >= 80.0 and aspect >= 2.70)
        medium = bool((not strong) and area >= 120.0 and 45.0 <= length_mm < 80.0 and aspect >= 4.00)
        tier = 3 if strong else (2 if medium else 1)
        severity = float(np.clip(
            0.45 * min(1.0, length_mm / 80.0)
            + 0.35 * min(1.0, (area / mask_area) / 0.015)
            + 0.20 * min(1.0, mean_score / 180.0),
            0.0, 1.0,
        ))
        priority = float(mean_score * math.sqrt(max(1.0, area)) * min(4.0, max(1.0, aspect)))
        item = {
            "area_px": area,
            "bbox": [x, y, w, h],
            "center_px": [cx, cy],
            "mean_score": mean_score,
            "max_score": max_score,
            "major_axis_px": geom["major_axis_px"],
            "minor_axis_px": geom["minor_axis_px"],
            "major_length_px": float(geom["major_length_px"]),
            "minor_length_px": float(geom["minor_length_px"]),
            "major_length_mm": length_mm,
            "minor_length_mm": float(geom["minor_length_mm"]),
            "linearity": aspect,
            "priority_score": priority,
            "d20_priority_tier": tier,
            "d21_severity": severity,
            "a119_cca_rule": "strong" if strong else ("medium_thin" if medium else "fine"),
            "d21_geometry": {
                "shape_class": "LINE",
                "center_board": geom["center_board"],
                "tangent_board": geom["tangent_board"],
                "normal_board": geom["normal_board"],
                "arc_length_mm": length_mm,
                "chord_length_mm": length_mm,
                "fit_confidence": float(np.clip((aspect - 1.0) / 4.0, 0.0, 1.0)),
            },
            "contour": contour,
        }
        candidates.append(item)
        kept[component > 0] = 255

    candidates.sort(key=lambda c: (int(c.get("d20_priority_tier", 0)), float(c.get("priority_score", 0.0))), reverse=True)
    # Keep enough components for finish judgment, not only the top action candidates.
    candidates = candidates[:max(12, int(args.wrinkle_heatmap_max_candidates))]
    inner_px = max(1, int(cv2.countNonZero(inner_mask)))
    ratio = float(cv2.countNonZero(kept)) / float(inner_px)
    summary = (
        f"A119 heatmap thr={threshold:.1f} roi={used_margin_mm:.1f}mm "
        f"active={ratio:.3f} blobs={len(candidates)} "
        f"strong={sum(c.get('a119_cca_rule') == 'strong' for c in candidates)} "
        f"medium={sum(c.get('a119_cca_rule') == 'medium_thin' for c in candidates)}"
    )
    return A119BottomHeatmapPlan(
        heatmap=heat_ready,
        inner_mask=inner_mask,
        binary=kept,
        candidates=candidates,
        threshold=float(threshold),
        wrinkle_ratio=ratio,
        status="OK",
        summary=summary,
        ready_heatmap=heat_ready,
        ready_inner_mask=inner_mask,
        ready_threshold=float(threshold),
        ready_roi_valid=True,
        d21v4_all_candidates=candidates,
        d21v4_residual_binary=kept,
        structure_ignore_mask=structure_mask,
        structure_info=structure_info,
        d23_waist_structure_ignored_count=int(structure_info.get("ignored_px", 0) > 0),
        d21v4_fine_ignored_count=sum(int(c.get("d20_priority_tier", 0)) <= 1 for c in candidates),
        highpass_abs=high.astype(np.float32),
        center_rise_ignore_mask=center_rise_mask,
        center_rise_info=center_rise_info,
    )



def _d24v5_waist_gather_report(cand: Dict[str, Any], heat: Any, obs: Any,
                               H: np.ndarray, metrics: Dict[str, Any], args) -> Dict[str, Any]:
    """Recognize elastic-waist gathers without deleting the whole upper pants area.

    A match must be short, remain inside a pose-relative upper band, touch either
    the waistband or the existing waistband-ignore boundary, and point radially
    away from its nearest waist-line anchor. Long/large components fail closed.
    """
    out: Dict[str, Any] = {
        "matched": False,
        "reason": "not waistband gather",
        "depth_mm": 0.0,
        "min_axial_mm": 0.0,
        "max_axial_mm": 0.0,
        "radial_error_deg": 180.0,
        "upper_support_ratio": 0.0,
    }
    if not bool(getattr(args, "d24v5_waist_gather_ignore", True)):
        return {**out, "reason": "disabled"}
    if obs is None or obs.pose is None or not obs.pose.valid or H is None:
        return {**out, "reason": "pose unavailable"}

    comp = candidate_component_mask(heat, cand)
    if comp is None:
        return {**out, "reason": "component unavailable"}
    pts = component_board_points(comp, H, max(300, int(getattr(args, "d24_seam_max_sample_points", 1800))))
    if len(pts) < 8:
        return {**out, "reason": "too few component points"}

    p = obs.pose
    try:
        wl = np.asarray(p.waist_left, np.float32).reshape(2)
        wc = np.asarray(p.waist_center, np.float32).reshape(2)
        wr = np.asarray(p.waist_right, np.float32).reshape(2)
        crotch = np.asarray(p.crotch, np.float32).reshape(2)
    except Exception:
        return {**out, "reason": "waist/crotch unavailable"}

    body_u = d23._safe_unit(crotch - wc)
    waist_u = d23._safe_unit(wr - wl)
    if abs(float(np.dot(body_u, waist_u))) > 0.55:
        waist_u = np.asarray([-body_u[1], body_u[0]], np.float32)
    waist_width = max(1.0, float(np.linalg.norm(wr - wl)))
    waist_to_crotch = max(1.0, float(np.linalg.norm(crotch - wc)))
    depth_limit = min(
        float(args.d24v5_waist_gather_depth_max_mm),
        waist_to_crotch * float(args.d24v5_waist_gather_depth_ratio),
    )
    # D23/D19 already removes a fixed waistband band. A residual gather may start
    # at that erased boundary rather than at axial=0, so allow contact with either.
    erased_forward = max(
        float(getattr(args, "d19_waistband_forward_mm", 0.0)),
        float(getattr(args, "d23_waist_structure_forward_mm", 0.0)),
    )
    connect_limit = min(depth_limit, erased_forward + float(args.d24v5_waist_gather_connect_mm))

    rel = pts - wc.reshape(1, 2)
    axial = rel @ body_u
    lateral = rel @ waist_u
    min_axial = float(np.min(axial))
    max_axial = float(np.max(axial))
    lateral_limit = 0.5 * waist_width + float(args.d24v5_waist_gather_side_expand_mm)
    in_upper = (
        (axial >= -8.0)
        & (axial <= depth_limit)
        & (np.abs(lateral) <= lateral_limit)
    )
    upper_support = float(np.count_nonzero(in_upper)) / float(max(1, len(pts)))

    geom = cand.get("d21_geometry", {}) or {}
    tangent = geom.get("tangent_board")
    if tangent is None:
        tangent = d23._pixel_axis_to_board(H, cand.get("center_px", [0.0, 0.0]), cand.get("major_axis_px", [1.0, 0.0]))
    tangent = d23._safe_unit(np.asarray(tangent if tangent is not None else [1.0, 0.0], np.float32))
    center_board = np.mean(pts, axis=0).astype(np.float32)
    center_rel = center_board - wc
    center_lateral = float(np.clip(np.dot(center_rel, waist_u), -0.5 * waist_width, 0.5 * waist_width))
    waist_anchor = wc + waist_u * center_lateral
    radial = d23._safe_unit(center_board - waist_anchor)
    radial_error = axis_angle_error_deg(tangent, radial)

    length = float(metrics.get("length_mm", 0.0))
    area_ratio = float(metrics.get("area_ratio", 0.0))
    max_length = min(
        float(args.d24v5_waist_gather_max_length_mm),
        waist_width * float(args.d24v5_waist_gather_max_length_ratio),
    )
    checks = {
        "touches_waist_boundary": min_axial <= connect_limit,
        "inside_upper_gather_band": max_axial <= depth_limit + 6.0,
        "upper_support": upper_support >= float(args.d24v5_waist_gather_min_upper_support),
        "radial_direction": radial_error <= float(args.d24v5_waist_gather_radial_angle_deg),
        "short": length <= max_length,
        "small_area": area_ratio <= float(args.d24v5_waist_gather_max_area_ratio),
    }
    matched = bool(all(checks.values()))
    failed = [k for k, v in checks.items() if not v]
    return {
        **out,
        "matched": matched,
        "reason": "waistband-connected radial gather" if matched else ",".join(failed),
        "checks": checks,
        "depth_mm": depth_limit,
        "connect_limit_mm": connect_limit,
        "min_axial_mm": min_axial,
        "max_axial_mm": max_axial,
        "radial_error_deg": radial_error,
        "upper_support_ratio": upper_support,
        "length_mm": length,
        "max_length_mm": max_length,
        "area_ratio": area_ratio,
        "waist_width_mm": waist_width,
        "waist_to_crotch_mm": waist_to_crotch,
        "anchor_board": [float(waist_anchor[0]), float(waist_anchor[1])],
        "center_board": [float(center_board[0]), float(center_board[1])],
    }


def _d24v6_fold_report(cand: Dict[str, Any], metrics: Dict[str, Any], heat: Any, args) -> Dict[str, Any]:
    """Block finish only for broad, contrast-supported physical folds.

    A normalized A119 heatmap can make pale fabric texture look strong. Therefore
    component area alone never blocks READY in v6. A candidate must be broad and
    have original-gray local contrast, unless it is extremely wide and large.
    """
    length = float(metrics.get("length_mm", 0.0))
    width = float(cand.get("minor_length_mm", 0.0))
    area_ratio = float(metrics.get("area_ratio", 0.0))
    severity = float(metrics.get("severity", 0.0))
    mean_response = float(metrics.get("mean_response", 0.0))
    contrast = _d24v6_component_contrast(cand, heat, args)
    mean_abs = float(contrast.get("mean_abs_contrast", 0.0))
    contrast_support = float(contrast.get("contrast_support", 0.0))
    photo_ok = bool(
        mean_abs >= float(args.d24v6_fold_min_abs_contrast)
        and contrast_support >= float(args.d24v6_fold_min_contrast_support)
    )
    broad_geometry = bool(
        length >= float(args.d24v5_fold_broad_min_length_mm)
        and width >= float(args.d24v5_fold_broad_min_width_mm)
        and area_ratio >= float(args.d24v5_fold_broad_min_area_ratio)
    )
    long_geometry = bool(
        length >= float(args.d24v5_fold_min_length_mm)
        and width >= float(args.d24v5_fold_min_width_mm)
        and area_ratio >= float(args.d24v5_fold_min_area_ratio)
    )
    normalized_strength = bool(
        severity >= float(args.d24v5_fold_min_severity)
        or mean_response >= float(args.d24v5_fold_min_mean_response)
    )
    extreme_geometry = bool(
        width >= float(args.d24v6_fold_extreme_width_mm)
        and area_ratio >= float(args.d24v6_fold_extreme_area_ratio)
    )
    broad_fold = bool(broad_geometry and photo_ok)
    long_deep_fold = bool(long_geometry and photo_ok and normalized_strength)
    extreme_fold = bool(extreme_geometry and mean_abs >= 0.70 * float(args.d24v6_fold_min_abs_contrast))
    reasons: List[str] = []
    if broad_fold:
        reasons.append("broad_contrast_fold")
    if long_deep_fold:
        reasons.append("long_deep_contrast_fold")
    if extreme_fold:
        reasons.append("extreme_wide_fold")
    return {
        "is_fold": bool(reasons),
        "reasons": reasons,
        "length_mm": length,
        "width_mm": width,
        "area_ratio": area_ratio,
        "severity": severity,
        "mean_response": mean_response,
        "mean_abs_contrast": mean_abs,
        "contrast_support": contrast_support,
        "photo_ok": photo_ok,
        "broad_geometry": broad_geometry,
        "long_geometry": long_geometry,
        "extreme_geometry": extreme_geometry,
        "broad_fold": broad_fold,
        "long_deep_fold": long_deep_fold,
        "extreme_fold": extreme_fold,
        "large_area_diagnostic_only": area_ratio >= float(args.d24v5_fold_large_area_ratio),
    }

def evaluate_d24_snapshot(obs: Any, heat: Any, H: np.ndarray, state: D24State, args) -> Dict[str, Any]:
    """One frozen photo -> pants-shape and fold-only finish decision."""
    state.evaluation_count += 1
    quality = observation_quality_report(obs, args)
    stability = {
        "good": True,
        "reason": "single frozen snapshot",
        "history_count": 1,
        "mask_area_rel": 0.0,
        "center_shift_mm": 0.0,
        "pose_axis_spread_deg": 0.0,
    }
    if not quality["good"]:
        state.ready_streak = 0
        return {
            "status": "REJUDGE", "reason": "OBSERVATION_INVALID",
            "evaluation": state.evaluation_count, "quality": quality,
            "stability": stability, "shape": {}, "wrinkle": {},
            "snapshot_mode": True,
        }

    # Pants silhouette/pose is the hard finish condition.
    shape = d23._d19_finish_shape_report(obs, args, H)
    if not bool(shape.get("shape_good", False)):
        state.ready_streak = 0
        return {
            "status": "NOT_READY_SHAPE", "reason": "PANTS_SHAPE_FAILED",
            "evaluation": state.evaluation_count, "quality": quality,
            "stability": stability, "shape": shape, "wrinkle": {},
            "snapshot_mode": True,
        }
    if heat is None:
        state.ready_streak = 0
        return {
            "status": "REJUDGE", "reason": "A119_HEATMAP_UNAVAILABLE",
            "evaluation": state.evaluation_count, "quality": quality,
            "stability": stability, "shape": shape, "wrinkle": {},
            "snapshot_mode": True,
        }

    robust = robust_heat_threshold(heat, args)
    waist_ref = _d24v2_waist_reference(obs, heat, H, robust, args)
    candidates = list(getattr(heat, "d21v4_all_candidates", [])) or list(getattr(heat, "candidates", []))

    fold_blockers: List[Dict[str, Any]] = []
    waist_gather_ignored: List[Dict[str, Any]] = []
    seam_ignored: List[Dict[str, Any]] = []
    fine_allowed: List[Dict[str, Any]] = []
    robust_rejected: List[Dict[str, Any]] = []
    t1: List[Dict[str, Any]] = []
    t2: List[Dict[str, Any]] = []

    for original in candidates:
        cand = dict(original)
        seam = seam_veto_report(cand, heat, obs, H, args)
        cand["d24_seam"] = seam
        if bool(seam.get("matched", False)):
            seam_ignored.append(cand)
            continue

        support = candidate_robust_support(cand, heat, float(robust["threshold"]))
        cand["d24_robust_support"] = support
        if support < float(args.d24_candidate_min_robust_support):
            robust_rejected.append(cand)
            continue

        metrics = _d24v2_candidate_metrics(cand, heat, obs, waist_ref)
        cand["d24v2_metrics"] = metrics

        gather = _d24v5_waist_gather_report(cand, heat, obs, H, metrics, args)
        cand["d24v5_waist_gather"] = gather
        if bool(gather.get("matched", False)):
            waist_gather_ignored.append(cand)
            continue

        fold = _d24v6_fold_report(cand, metrics, heat, args)
        cand["d24v6_fold"] = fold
        if bool(fold.get("is_fold", False)):
            fold_blockers.append(cand)
        else:
            fine_allowed.append(cand)

        tier = int(metrics.get("tier", 0))
        if tier <= 1:
            t1.append(cand)
        elif tier == 2:
            t2.append(cand)

    mask_area = max(1.0, float(obs.mask.area_px))
    effective_area = max(1.0, float(cv2.countNonZero(heat.inner_mask)))
    blocker_area = float(sum(float(c.get("area_px", 0.0)) for c in fold_blockers))
    blocker_ratio = blocker_area / effective_area
    max_blob_ratio = max([float(c.get("area_px", 0.0)) / mask_area for c in fold_blockers] or [0.0])
    max_severity = max([float((c.get("d24v2_metrics", {}) or {}).get("severity", 0.0)) for c in fold_blockers] or [0.0])
    checks = {"fold_count": len(fold_blockers) <= int(args.finish_max_t3_count)}
    wrinkle_good = bool(all(checks.values()))

    wrinkle_report = {
        "policy": "PANTS_SHAPE_PLUS_REAL_FOLD_ONLY_WITH_CENTER_RISE_IGNORE",
        "good": wrinkle_good,
        "checks": checks,
        "t3_count": len(fold_blockers),
        "fold_count": len(fold_blockers),
        "t2_count": len(t2),
        "t1_allowed_count": len(t1),
        "fine_allowed_count": len(fine_allowed),
        "relative_allowed_count": 0,
        "non_major_allowed_count": len(fine_allowed),
        "waist_gather_ignored_count": len(waist_gather_ignored),
        "center_rise_ignored_px": int((getattr(heat, "center_rise_info", {}) or {}).get("ignored_px", 0)),
        "seam_ignored_count": len(seam_ignored),
        "robust_rejected_count": len(robust_rejected),
        "waist_structure_ignored_count": int(getattr(heat, "d23_waist_structure_ignored_count", 0)),
        "fine_ignored_count": len(fine_allowed) + int(getattr(heat, "d21v4_fine_ignored_count", 0)),
        "max_severity": max_severity,
        "actionable_ratio": blocker_ratio,
        "max_blob_ratio": max_blob_ratio,
        "waist_reference": waist_ref,
        "robust": robust,
        "a119_summary": str(getattr(heat, "summary", "")),
        "limits": {
            "max_fold_count": int(args.finish_max_t3_count),
            "gather_depth_ratio": float(args.d24v5_waist_gather_depth_ratio),
            "gather_radial_angle_deg": float(args.d24v5_waist_gather_radial_angle_deg),
            "fold_min_length_mm": float(args.d24v5_fold_min_length_mm),
            "fold_min_width_mm": float(args.d24v5_fold_min_width_mm),
            "fold_min_area_ratio": float(args.d24v5_fold_min_area_ratio),
            "fold_large_area_ratio_diagnostic_only": float(args.d24v5_fold_large_area_ratio),
            "fold_min_abs_contrast": float(args.d24v6_fold_min_abs_contrast),
            "center_rise_half_width_mm": float(args.d24v6_center_rise_half_width_mm),
        },
        "remaining": [k for k, v in checks.items() if not v],
        "t1": t1,
        "t2": t2,
        "t3": fold_blockers,
        "major_blockers": fold_blockers,
        "fold_blockers": fold_blockers,
        "waist_gather_ignored": waist_gather_ignored,
        "relative_allowed": [],
        "non_major_allowed": fine_allowed,
        "fine_allowed": fine_allowed,
        "seam_ignored": seam_ignored,
        "robust_rejected": robust_rejected,
    }

    if not wrinkle_good:
        state.ready_streak = 0
        return {
            "status": "NOT_READY_WRINKLE", "reason": "REAL_FOLD_REMAINS",
            "evaluation": state.evaluation_count, "quality": quality,
            "stability": stability, "shape": shape, "wrinkle": wrinkle_report,
            "ready_streak": 0, "ready_required": 1, "snapshot_mode": True,
        }

    state.ready_streak = 1
    return {
        "status": "READY_GOOD_ENOUGH", "reason": "PANTS_SHAPE_OK_AND_NO_REAL_FOLD",
        "evaluation": state.evaluation_count, "quality": quality,
        "stability": stability, "shape": shape, "wrinkle": wrinkle_report,
        "ready_streak": 1, "ready_required": 1, "snapshot_mode": True,
    }

def evaluate_frame_snapshot(frame: np.ndarray, H: np.ndarray, seg_model, pose_model,
                            state: D24State, args, cfg) -> Tuple[Any, Any, Dict[str, Any], np.ndarray]:
    obs = d23.infer_bottom_observation(seg_model, pose_model, frame, H, args, cfg)
    heat = build_a119_bottom_heatmap(frame, obs, H, args) if obs is not None and obs.mask is not None else None
    report = evaluate_d24_snapshot(obs, heat, H, state, args)
    overlay = draw_d24_overlay(frame, obs, heat, report, H, cfg, args)
    put_text(overlay, "FROZEN SNAPSHOT / SHAPE + FOLD ONLY", (25, overlay.shape[0] - 22), (255, 255, 255), 0.62, 2)
    return obs, heat, report, overlay


def _save_captured_source(frame: np.ndarray, args, status: str = "CAPTURE") -> str:
    out_dir = Path(args.snapshot_dir)
    out_dir.mkdir(parents=True, exist_ok=True)
    ts = time.strftime("%Y%m%d_%H%M%S")
    path = out_dir / f"d24v6_{ts}_{status}_source.jpg"
    cv2.imwrite(str(path), frame)
    return str(path)


def run_single_image_snapshot(args, config, cfg, H, seg_model, pose_model) -> int:
    frame = cv2.imread(args.image)
    if frame is None:
        print(f"[D24V3-ERROR] cannot read image: {args.image}")
        return 2
    if H is None:
        print("[D24V3-ERROR] Homography is required for --image. Load --hfile first.")
        return 2
    state = D24State(history=collections.deque(maxlen=1))
    obs, heat, report, overlay = evaluate_frame_snapshot(frame, H, seg_model, pose_model, state, args, cfg)
    state.latest_obs, state.latest_heat = obs, heat
    state.latest_report, state.latest_overlay = report, overlay
    state.latest_status = str(report.get("status", "REJUDGE"))
    state.latest_eval_frame = frame.copy()
    state.latest_h = H.copy()
    cv2.imwrite(args.output, overlay)
    print_report(report)
    print(f"[D24V3] frozen result saved: {args.output}")
    append_jsonl(args.log_jsonl, report)
    return 0
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
