ChoBeomGyu25/2026ESWContest_free_-/SW/Jetson/preprocessing/lower/dual/undistort/step_e49_bottom_perception.py

#!/usr/bin/env python3
# -*- coding: utf-8 -*-
"""
step_e49_bottom_perception.py

E49 combined bottom-garment perception with empty-board and strict ArUco-board ROI sanitation.

Extracted from step_e43_bottom_keypoint_wiggle_test.py and intentionally limited to:
  - segmentation and garment-mask selection
  - glare/specular suppression
  - wrinkle Heatmap and local-shadow analysis
  - bottom pose inference, TTA, consensus, and temporal stabilization
  - mask topology, PCA/oriented-rectangle geometry
  - crotch concavity and waistband evidence
  - mask-primary/fallback landmark reconstruction
  - final pose geometry scoring
  - construction of BottomObservation

Robot action classification, path planning, serial execution, camera runtime, and UI are
not included. The public boundary of this module is infer_bottom_observation(), which
returns perception/geometry results without selecting or executing an action.

E49 preserves the E45 closed-crotch pipeline and the E47 empty folding-board
baseline stage. It additionally constrains segmentation masks to the quadrilateral
formed by the configured ArUco marker centers, excludes marker patches, and performs
connected-component/Pose-consistency sanitation. Strict ROI failure never falls back
to the unsanitized YOLO mask, so unsafe off-board detections cannot drive motion.
"""

from __future__ import annotations

import math
import threading
import time
from dataclasses import dataclass, field
from typing import Any, Dict, List, Optional, Sequence, Tuple

import cv2
import numpy as np

CODE_VERSION = "E49"
CODE_BUILD_ID = "E49-BOTTOM-PERCEPTION-BOARD-ROI-V1-20260724"
SOURCE_BASELINE = "step_e47_bottom_perception.py"


BOTTOM_POSE_KPT_NAMES = [
    "waist_img_left",       # 0
    "waist_center",         # 1
    "waist_img_right",      # 2
    "crotch",               # 3
    "img_left_hem_outer",   # 4
    "img_left_hem_inner",   # 5
    "img_right_hem_inner",  # 6
    "img_right_hem_outer",  # 7
]
BOTTOM_POSE_KPT = {name: i for i, name in enumerate(BOTTOM_POSE_KPT_NAMES)}
BOTTOM_POSE_KPT_SHORT_NAMES = [
    "WAIST_L", "WAIST_C", "WAIST_R", "CROTCH",
    "L_HEM_OUT", "L_HEM_IN", "R_HEM_IN", "R_HEM_OUT",
]
HFLIP_REMAP = np.asarray([2, 1, 0, 3, 7, 6, 5, 4], dtype=np.int32)

class BottomActionDecision:
    action: str
    reason: str
    confidence: float = 0.0
    metrics: Dict[str, Any] = field(default_factory=dict)


@dataclass
class BottomPoseBoard:
    keypoints_board: Dict[str, Tuple[float, float]]
    keypoints_px: Dict[str, Tuple[float, float]]
    keypoint_conf: Dict[str, float]
    waist_left: np.ndarray
    waist_center: np.ndarray
    waist_right: np.ndarray
    crotch: np.ndarray
    left_hem_center: np.ndarray
    right_hem_center: np.ndarray
    lower_center: np.ndarray
    pose_center: np.ndarray
    waist_angle_deg: float
    pants_axis_angle_deg: float
    pants_axis_len_mm: float
    waist_width_mm: float
    hem_gap_mm: float
    valid: bool
    reason: str
    inference_status: str = ""
    geometry_reliable: bool = False
    geometry_score: float = 0.0
    recovery_required: bool = False
    geometry_metrics: Dict[str, Any] = field(default_factory=dict)
    crotch_state: str = "UNKNOWN"
    crotch_confidence: float = 0.0
    polarity_metrics: Dict[str, Any] = field(default_factory=dict)
    pre_spread_required: bool = False


@dataclass
class BottomMaskBoard:
    mask_u8: np.ndarray
    contour: np.ndarray
    area_px: float
    center_px: np.ndarray
    center_board: np.ndarray
    class_name: str
    confidence: float
    solidity: float
    empty_baseline_info: Dict[str, Any] = field(default_factory=dict)
    board_roi_info: Dict[str, Any] = field(default_factory=dict)


@dataclass
class BottomObservation:
    pose: Optional[BottomPoseBoard]
    mask: Optional[BottomMaskBoard]
    fused_center_board: Optional[np.ndarray]
    valid: bool
    reason: str
    frame: Optional[np.ndarray] = None
    wrinkle: Optional[Dict[str, Any]] = None
    action_decision: Optional[BottomActionDecision] = None
    shape_debug: Optional[Dict[str, Any]] = None
    glare: Optional[Dict[str, Any]] = None
    crotch_state: str = "UNKNOWN"
    pants_polarity: Optional[Dict[str, Any]] = None
    pre_spread_required: bool = False
    empty_baseline: Optional[Dict[str, Any]] = None
    board_roi: Optional[Dict[str, Any]] = None

def pixel_to_board(H: np.ndarray, u: float, v: float) -> Tuple[float, float]:
    p = np.array([[[float(u), float(v)]]], dtype=np.float32)
    out = cv2.perspectiveTransform(p, H)
    return float(out[0, 0, 0]), float(out[0, 0, 1])


def board_to_pixel(H: np.ndarray, bx: float, by: float) -> Optional[Tuple[float, float]]:
    try:
        Hinv = np.linalg.inv(H)
        p = np.array([[[float(bx), float(by)]]], dtype=np.float32)
        out = cv2.perspectiveTransform(p, Hinv)
        return float(out[0, 0, 0]), float(out[0, 0, 1])
    except Exception:
        return None


def get_dictionary(name: str = "DICT_4X4_50"):
    if not hasattr(cv2.aruco, name):
        raise ValueError(f"Unknown ArUco dictionary: {name}")
    return cv2.aruco.getPredefinedDictionary(getattr(cv2.aruco, name))


def make_aruco_detector(dictionary):
    if hasattr(cv2.aruco, "ArucoDetector"):
        params = cv2.aruco.DetectorParameters()
        return cv2.aruco.ArucoDetector(dictionary, params)
    params = cv2.aruco.DetectorParameters_create()
    return dictionary, params


def detect_markers(frame: np.ndarray, detector_obj):
    if isinstance(detector_obj, tuple):
        dictionary, params = detector_obj
        return cv2.aruco.detectMarkers(frame, dictionary, parameters=params)
    return detector_obj.detectMarkers(frame)


def compute_homography(corners, ids, marker_board_mm: Dict[str, List[float]], required_ids: Sequence[int]):
    if ids is None:
        return None, {}
    centers = {}
    for c, marker_id in zip(corners, ids.flatten()):
        pts = c.reshape(4, 2)
        centers[int(marker_id)] = pts.mean(axis=0)
    if not all(i in centers for i in required_ids):
        return None, centers
    img_pts = np.array([centers[i] for i in required_ids], dtype=np.float32)
    board_pts = np.array([marker_board_mm[str(i)] for i in required_ids], dtype=np.float32)
    H, _ = cv2.findHomography(img_pts, board_pts)
    return H, centers


def normalize_angle_deg(angle: float) -> float:
    return float((float(angle) + 180.0) % 360.0 - 180.0)


def unit_vec(v: np.ndarray, fallback=(1.0, 0.0)) -> np.ndarray:
    arr = np.asarray(v, dtype=np.float32).reshape(2)
    n = float(np.linalg.norm(arr))
    if n < 1e-6:
        return np.asarray(fallback, dtype=np.float32)
    return arr / n

def result_mask_to_u8(result, index: int, image_shape) -> Optional[np.ndarray]:
    if getattr(result, "masks", None) is None or result.masks is None:
        return None
    h, w = image_shape[:2]
    try:
        data = result.masks.data[index].detach().cpu().numpy()
        if data.shape[:2] != (h, w):
            data = cv2.resize(data, (w, h), interpolation=cv2.INTER_LINEAR)
        return ((data > 0.5).astype(np.uint8) * 255)
    except Exception:
        return None


def parse_class_names(raw: Any) -> List[str]:
    if raw is None:
        return []
    if isinstance(raw, (list, tuple)):
        items = raw
    else:
        items = str(raw).split(",")
    out = []
    for item in items:
        name = str(item).strip()
        if name and name not in out:
            out.append(name)
    return out



def _empty_baseline_board_shift_px(H_current: np.ndarray, H_saved: np.ndarray,
                                   board_points: Sequence[Sequence[float]]) -> Optional[Dict[str, float]]:
    distances: List[float] = []
    try:
        for raw in board_points:
            bx, by = float(raw[0]), float(raw[1])
            p_now = board_to_pixel(H_current, bx, by)
            p_old = board_to_pixel(H_saved, bx, by)
            if p_now is None or p_old is None:
                continue
            distances.append(float(np.linalg.norm(np.asarray(p_now) - np.asarray(p_old))))
    except Exception:
        return None
    if not distances:
        return None
    return {
        "mean_px": float(np.mean(distances)),
        "max_px": float(np.max(distances)),
    }


def _board_roi_from_reference(H: np.ndarray, board_points: Sequence[Sequence[float]],
                              image_shape) -> np.ndarray:
    h, w = image_shape[:2]
    roi = np.zeros((h, w), dtype=np.uint8)
    pixels: List[List[int]] = []
    for raw in board_points:
        p = board_to_pixel(H, float(raw[0]), float(raw[1]))
        if p is not None:
            pixels.append([int(round(p[0])), int(round(p[1]))])
    if len(pixels) >= 3:
        hull = cv2.convexHull(np.asarray(pixels, dtype=np.int32).reshape(-1, 1, 2))
        cv2.fillConvexPoly(roi, hull, 255)
    else:
        roi[:] = 255
    return roi



def _runtime_board_marker_map(args) -> Tuple[Dict[str, Sequence[float]], List[int], str]:
    """Return Config-provided marker geometry without using a legacy board fallback."""
    marker_map = getattr(args, "_board_marker_map", None) if args is not None else None
    required_ids = getattr(args, "_board_required_ids", None) if args is not None else None
    if not isinstance(marker_map, dict) or len(marker_map) < 3:
        return {}, [], "marker geometry unavailable"
    ids: List[int] = []
    for value in (required_ids or [0, 1, 2, 3]):
        try:
            marker_id = int(value)
        except Exception:
            continue
        if str(marker_id) in marker_map or marker_id in marker_map:
            ids.append(marker_id)
    if len(ids) < 3:
        return marker_map, ids, "fewer than three configured markers"
    return marker_map, ids, str(getattr(args, "_board_roi_source", "folding-board-config"))


def build_board_roi_polygon_px(image_shape, H: Optional[np.ndarray], args) -> Tuple[Optional[np.ndarray], List[Tuple[int, int]], Dict[str, Any]]:
    """Project configured marker centers into the camera frame and build their convex hull."""
    h, w = image_shape[:2]
    marker_map, required_ids, source = _runtime_board_marker_map(args)
    info: Dict[str, Any] = {
        "enabled": bool(getattr(args, "board_roi", True)),
        "source": source,
        "required_ids": list(required_ids),
        "marker_points_px": [],
        "polygon_px": None,
        "valid": False,
        "reason": "not evaluated",
    }
    if not info["enabled"]:
        info.update({"valid": True, "reason": "disabled"})
        return None, [], info
    if H is None:
        info["reason"] = "homography missing"
        return None, [], info
    if len(required_ids) < 3:
        info["reason"] = source
        return None, [], info
    points: List[Tuple[int, int]] = []
    used_ids: List[int] = []
    for marker_id in required_ids:
        raw = marker_map.get(str(marker_id), marker_map.get(marker_id))
        if raw is None or len(raw) < 2:
            continue
        q = board_to_pixel(np.asarray(H, dtype=np.float32), float(raw[0]), float(raw[1]))
        if q is None or not np.all(np.isfinite(q)):
            continue
        x = int(np.clip(round(float(q[0])), -2 * w, 3 * w))
        y = int(np.clip(round(float(q[1])), -2 * h, 3 * h))
        points.append((x, y))
        used_ids.append(int(marker_id))
    info["marker_points_px"] = [[int(x), int(y)] for x, y in points]
    info["used_ids"] = used_ids
    if len(points) < 3:
        info["reason"] = f"only {len(points)} marker projections available"
        return None, points, info
    hull = cv2.convexHull(np.asarray(points, dtype=np.int32).reshape(-1, 1, 2)).reshape(-1, 2)
    info.update({
        "valid": True,
        "reason": "OK",
        "polygon_px": hull.astype(int).tolist(),
    })
    return hull.astype(np.int32), points, info


def build_board_valid_mask(image_shape, H: Optional[np.ndarray], args) -> Tuple[np.ndarray, Dict[str, Any]]:
    """Build the strict ArUco-board valid region and remove marker patches/borders."""
    h, w = image_shape[:2]
    enabled = bool(getattr(args, "board_roi", True))
    strict = bool(getattr(args, "board_roi_strict", True))
    border = max(0, int(getattr(args, "board_frame_border_exclude_px", 8)))
    polygon, marker_points, info = build_board_roi_polygon_px(image_shape, H, args)
    info.update({"strict": strict, "border_exclude_px": border})
    if not enabled:
        valid = np.full((h, w), 255, dtype=np.uint8)
    elif polygon is None or len(polygon) < 3:
        valid = np.zeros((h, w), dtype=np.uint8) if strict else np.full((h, w), 255, dtype=np.uint8)
        info["reason"] = f"{info.get('reason', 'ROI unavailable')}; {'strict block' if strict else 'non-strict full-frame fallback'}"
        info["valid"] = not strict
    else:
        valid = np.zeros((h, w), dtype=np.uint8)
        cv2.fillConvexPoly(valid, polygon, 255)
        expand = max(0, int(getattr(args, "board_roi_expand_px", 0)))
        if expand > 0:
            k = 2 * expand + 1
            valid = cv2.dilate(valid, cv2.getStructuringElement(cv2.MORPH_ELLIPSE, (k, k)))
        info["expand_px"] = expand

    marker_radius = max(0, int(getattr(args, "board_marker_exclusion_radius_px", 30)))
    if marker_radius > 0:
        for point in marker_points:
            cv2.circle(valid, tuple(map(int, point)), marker_radius, 0, -1)
    if border > 0:
        valid[:border, :] = 0
        valid[-border:, :] = 0
        valid[:, :border] = 0
        valid[:, -border:] = 0
    info.update({
        "marker_exclusion_radius_px": marker_radius,
        "valid_pixel_count": int(cv2.countNonZero(valid)),
        "valid_frame_ratio": float(cv2.countNonZero(valid)) / float(max(1, h * w)),
    })
    return valid, info


def _mask_iou_u8(a: np.ndarray, b: np.ndarray) -> float:
    if a is None or b is None or a.shape != b.shape:
        return 0.0
    aa, bb = np.asarray(a) > 0, np.asarray(b) > 0
    union = int(np.count_nonzero(aa | bb))
    return float(np.count_nonzero(aa & bb)) / float(union) if union > 0 else 0.0


def sanitize_board_mask_u8(mask_u8: np.ndarray, H: Optional[np.ndarray], image_shape, args,
                           pose: Optional[BottomPoseBoard] = None,
                           require_pose: bool = False,
                           select_component: bool = True) -> Tuple[Optional[np.ndarray], Dict[str, Any]]:
    """Clip a candidate to the ArUco board and select one safe connected component."""
    raw = ((np.asarray(mask_u8, dtype=np.uint8) > 0).astype(np.uint8) * 255)
    raw_count = int(cv2.countNonZero(raw))
    info: Dict[str, Any] = {
        "enabled": bool(getattr(args, "board_roi", True)),
        "strict": bool(getattr(args, "board_roi_strict", True)),
        "valid": False,
        "accepted": False,
        "reason": "raw mask missing" if raw_count <= 0 else "not evaluated",
        "raw_area_px": raw_count,
        "require_pose": bool(require_pose),
        "select_component": bool(select_component),
    }
    if raw_count <= 0:
        return None, info
    if not info["enabled"]:
        info.update({"valid": True, "accepted": True, "reason": "board ROI disabled", "selected_area_px": raw_count})
        return raw, info

    valid_mask, roi_info = build_board_valid_mask(image_shape, H, args)
    info["roi"] = roi_info
    if int(cv2.countNonZero(valid_mask)) <= 0:
        info["reason"] = f"board ROI unavailable: {roi_info.get('reason', '')}"
        if info["strict"]:
            return None, info
        info.update({"valid": True, "accepted": True, "reason": "non-strict raw fallback", "selected_area_px": raw_count})
        return raw, info

    mask = cv2.bitwise_and(raw, valid_mask)
    board_count = int(cv2.countNonZero(mask))
    info["board_clipped_area_px"] = board_count
    info["board_keep_ratio"] = float(board_count) / float(max(1, raw_count))
    if board_count <= 0:
        info["reason"] = "mask has no pixels inside ArUco board ROI"
        return None, info

    def _morph_kernel(value: Any) -> np.ndarray:
        k = max(1, int(value))
        if k % 2 == 0:
            k += 1
        return cv2.getStructuringElement(cv2.MORPH_ELLIPSE, (k, k))

    mask = cv2.morphologyEx(mask, cv2.MORPH_OPEN, _morph_kernel(getattr(args, "board_mask_open_px", 3)))
    mask = cv2.morphologyEx(mask, cv2.MORPH_CLOSE, _morph_kernel(getattr(args, "board_mask_close_px", 5)))
    h, w = image_shape[:2]
    num, labels, stats, _ = cv2.connectedComponentsWithStats((mask > 0).astype(np.uint8), 8)
    if num <= 1:
        info["reason"] = "no component after board/marker exclusion"
        return None, info

    pose_points: List[Tuple[float, float]] = []
    if pose is not None and isinstance(getattr(pose, "keypoints_px", None), dict):
        pose_points = [(float(x), float(y)) for x, y in pose.keypoints_px.values()]
    pose_hull_area = 0.0
    if len(pose_points) >= 3:
        pose_hull = cv2.convexHull(np.asarray(pose_points, dtype=np.float32).reshape(-1, 1, 2))
        pose_hull_area = float(cv2.contourArea(pose_hull))

    min_component = max(300, int(getattr(args, "board_mask_min_component_px", 1200)))
    min_inside = max(0, int(getattr(args, "board_mask_min_pose_inside", 5)))
    pose_gate_active = bool(require_pose and len(pose_points) >= max(1, min_inside))
    info["pose_point_count"] = int(len(pose_points))
    info["pose_gate_active"] = pose_gate_active
    max_frame_ratio = float(np.clip(getattr(args, "board_mask_max_frame_ratio", 0.72), 0.01, 1.0))
    max_pose_hull_ratio = max(1.0, float(getattr(args, "board_mask_max_pose_hull_ratio", 6.0)))
    best_label = None
    accepted_labels: List[int] = []
    best_score = -1e30
    best_diag: Dict[str, Any] = {}
    reject_counts = {"small": 0, "frame": 0, "pose": 0, "hull": 0}
    for label in range(1, int(num)):
        area = int(stats[label, cv2.CC_STAT_AREA])
        if area < min_component:
            reject_counts["small"] += 1
            continue
        frame_ratio = float(area) / float(max(1, h * w))
        if frame_ratio > max_frame_ratio:
            reject_counts["frame"] += 1
            continue
        comp = labels == label
        inside = 0
        for x, y in pose_points:
            xi, yi = int(round(x)), int(round(y))
            if 0 <= xi < w and 0 <= yi < h and bool(comp[yi, xi]):
                inside += 1
        if pose_gate_active and inside < min_inside:
            reject_counts["pose"] += 1
            continue
        hull_ratio = float(area) / max(1.0, pose_hull_area) if pose_hull_area > 1.0 else 1.0
        if pose_hull_area > 1.0 and hull_ratio > max_pose_hull_ratio:
            reject_counts["hull"] += 1
            continue
        accepted_labels.append(int(label))
        x = int(stats[label, cv2.CC_STAT_LEFT])
        y = int(stats[label, cv2.CC_STAT_TOP])
        ww = int(stats[label, cv2.CC_STAT_WIDTH])
        hh = int(stats[label, cv2.CC_STAT_HEIGHT])
        border_touch = int(x <= 2) + int(y <= 2) + int(x + ww >= w - 2) + int(y + hh >= h - 2)
        score = area - border_touch * 500000.0
        if pose_points:
            score += inside * 1000000.0 - max(0.0, hull_ratio - 3.0) * 30000.0
        if score > best_score:
            best_score = score
            best_label = label
            best_diag = {
                "pose_inside": int(inside), "area_px": int(area),
                "frame_ratio": frame_ratio, "pose_hull_ratio": hull_ratio,
                "border_touch": int(border_touch),
            }
    info["rejected_components"] = reject_counts
    info["component_count"] = int(num - 1)
    if not accepted_labels or best_label is None:
        info["reason"] = "no safe board/Pose-consistent component"
        return None, info
    if select_component:
        selected = ((labels == int(best_label)).astype(np.uint8) * 255)
        info.update(best_diag)
        reason = "OK selected best board/Pose component"
    else:
        selected = (np.isin(labels, np.asarray(accepted_labels, dtype=np.int32)).astype(np.uint8) * 255)
        info.update({
            "pose_inside": 0,
            "area_px": int(cv2.countNonZero(selected)),
            "frame_ratio": float(cv2.countNonZero(selected)) / float(max(1, h * w)),
            "pose_hull_ratio": 1.0,
            "border_touch": 0,
            "retained_component_count": int(len(accepted_labels)),
        })
        reason = "OK retained pre-Pose board components"
    selected_count = int(cv2.countNonZero(selected))
    info.update({
        "valid": True,
        "accepted": True,
        "reason": reason,
        "selected_area_px": selected_count,
        "selected_keep_ratio_from_raw": float(selected_count) / float(max(1, raw_count)),
    })
    return selected, info


def rebuild_bottom_mask_from_u8(mask_u8: np.ndarray, H: np.ndarray, raw: BottomMaskBoard,
                                board_info: Dict[str, Any]) -> Optional[BottomMaskBoard]:
    mask = ((np.asarray(mask_u8, dtype=np.uint8) > 0).astype(np.uint8) * 255)
    contours, _ = cv2.findContours(mask, cv2.RETR_EXTERNAL, cv2.CHAIN_APPROX_SIMPLE)
    if not contours:
        return None
    contour = max(contours, key=cv2.contourArea)
    area = float(cv2.contourArea(contour))
    if area <= 10.0:
        return None
    clean = np.zeros_like(mask)
    cv2.drawContours(clean, [contour], -1, 255, -1)
    moments = cv2.moments(contour)
    if abs(moments["m00"]) > 1e-6:
        center_px = np.asarray([moments["m10"] / moments["m00"], moments["m01"] / moments["m00"]], dtype=np.float32)
    else:
        center_px = contour.reshape(-1, 2).astype(np.float32).mean(axis=0)
    bx, by = pixel_to_board(H, float(center_px[0]), float(center_px[1]))
    hull = cv2.convexHull(contour)
    hull_area = float(cv2.contourArea(hull))
    return BottomMaskBoard(
        mask_u8=clean,
        contour=contour,
        area_px=area,
        center_px=center_px,
        center_board=np.asarray([bx, by], dtype=np.float32),
        class_name=str(raw.class_name),
        confidence=float(raw.confidence),
        solidity=float(area / hull_area if hull_area > 1.0 else 0.0),
        empty_baseline_info=dict(getattr(raw, "empty_baseline_info", {}) or {}),
        board_roi_info=dict(board_info or {}),
    )


def evaluate_empty_baseline_candidate(frame: np.ndarray, candidate_mask: np.ndarray,
                                      H: Optional[np.ndarray], args) -> Tuple[Optional[np.ndarray], Dict[str, Any]]:
    """Conservatively validate/refine one YOLO mask against an empty-board reference.

    The reference never creates a garment mask by itself. It may reject a YOLO
    candidate that is nearly identical to the empty folding board, or refine an
    accepted candidate when the changed support remains sufficiently large.
    """
    info: Dict[str, Any] = {
        "enabled": bool(getattr(args, "empty_baseline_veto", True)),
        "available": False,
        "compatible": False,
        "active": False,
        "accepted": True,
        "rejected": False,
        "refined": False,
        "reason": "disabled",
        "mean_ab_diff": 0.0,
        "changed_ab_ratio": 0.0,
        "combined_ratio": 0.0,
        "refined_keep_ratio": 1.0,
        "illumination_l_shift": 0.0,
        "homography_mean_shift_px": None,
        "homography_max_shift_px": None,
    }
    mask = np.asarray(candidate_mask, dtype=np.uint8)
    if not info["enabled"]:
        return mask, info

    baseline = getattr(args, "_empty_baseline_bgr", None)
    baseline_h = getattr(args, "_empty_baseline_h", None)
    board_points = getattr(args, "_empty_baseline_board_points", None)
    if baseline is None:
        info["reason"] = "baseline unavailable"
        if bool(getattr(args, "empty_baseline_require", False)):
            info.update({"accepted": False, "rejected": True})
            return None, info
        return mask, info
    info["available"] = True
    baseline = np.asarray(baseline, dtype=np.uint8)
    if baseline.shape != frame.shape:
        info["reason"] = f"resolution mismatch baseline={baseline.shape} current={frame.shape}"
        if bool(getattr(args, "empty_baseline_require", False)):
            info.update({"accepted": False, "rejected": True})
            return None, info
        return mask, info
    if H is None or baseline_h is None or not board_points:
        info["reason"] = "baseline homography metadata unavailable"
        if bool(getattr(args, "empty_baseline_require", False)):
            info.update({"accepted": False, "rejected": True})
            return None, info
        return mask, info

    shift = _empty_baseline_board_shift_px(
        np.asarray(H, dtype=np.float32), np.asarray(baseline_h, dtype=np.float32), board_points,
    )
    if shift is None:
        info["reason"] = "homography compatibility check failed"
        if bool(getattr(args, "empty_baseline_require", False)):
            info.update({"accepted": False, "rejected": True})
            return None, info
        return mask, info
    info["homography_mean_shift_px"] = float(shift["mean_px"])
    info["homography_max_shift_px"] = float(shift["max_px"])
    max_h_shift = max(0.5, float(getattr(args, "empty_baseline_max_h_shift_px", 8.0)))
    if float(shift["max_px"]) > max_h_shift:
        info["reason"] = (
            f"homography moved max={float(shift['max_px']):.1f}px > {max_h_shift:.1f}px; recapture E baseline"
        )
        if bool(getattr(args, "empty_baseline_require", False)):
            info.update({"accepted": False, "rejected": True})
            return None, info
        return mask, info
    info["compatible"] = True

    candidate = mask > 0
    candidate_count = int(np.count_nonzero(candidate))
    if candidate_count <= 0:
        info.update({"accepted": False, "rejected": True, "reason": "empty YOLO mask"})
        return None, info

    base_lab = cv2.cvtColor(baseline, cv2.COLOR_BGR2LAB).astype(np.float32)
    curr_lab = cv2.cvtColor(frame, cv2.COLOR_BGR2LAB).astype(np.float32)
    board_roi = _board_roi_from_reference(np.asarray(H, dtype=np.float32), board_points, frame.shape)

    # Estimate a small global illumination shift from board pixels outside the
    # candidate. This preserves dark/gray clothing contrast while compensating
    # for minor lamp or exposure drift.
    exclusion_px = max(3, int(getattr(args, "empty_baseline_illumination_exclusion_px", 17)))
    exclusion_kernel = cv2.getStructuringElement(cv2.MORPH_ELLIPSE, (exclusion_px | 1, exclusion_px | 1))
    excluded = cv2.dilate(mask, exclusion_kernel, iterations=1) > 0
    illumination_support = (board_roi > 0) & (~excluded)
    l_shift = 0.0
    if int(np.count_nonzero(illumination_support)) >= 500:
        l_delta = curr_lab[:, :, 0] - base_lab[:, :, 0]
        l_shift = float(np.median(l_delta[illumination_support]))
        limit = max(0.0, float(getattr(args, "empty_baseline_max_l_shift", 20.0)))
        l_shift = float(np.clip(l_shift, -limit, limit))
    info["illumination_l_shift"] = l_shift

    d_l = np.abs((curr_lab[:, :, 0] - l_shift) - base_lab[:, :, 0])
    d_a = curr_lab[:, :, 1] - base_lab[:, :, 1]
    d_b = curr_lab[:, :, 2] - base_lab[:, :, 2]
    d_ab = np.sqrt(d_a * d_a + d_b * d_b)
    l_weight = max(0.0, float(getattr(args, "empty_baseline_l_weight", 0.25)))
    combined = l_weight * d_l + d_ab

    ab_threshold = max(0.0, float(getattr(args, "empty_change_ab_threshold", 10.0)))
    combined_threshold = max(0.0, float(getattr(args, "empty_change_combined_threshold", 14.0)))
    changed_ab = d_ab >= ab_threshold
    changed_combined = combined >= combined_threshold
    changed = (changed_ab | changed_combined).astype(np.uint8) * 255
    changed = cv2.bitwise_and(changed, board_roi)
    morph_px = max(1, int(getattr(args, "empty_change_morph_px", 5))) | 1
    morph_kernel = cv2.getStructuringElement(cv2.MORPH_ELLIPSE, (morph_px, morph_px))
    changed = cv2.morphologyEx(changed, cv2.MORPH_OPEN, morph_kernel, iterations=1)
    changed = cv2.morphologyEx(changed, cv2.MORPH_CLOSE, morph_kernel, iterations=2)

    info["mean_ab_diff"] = float(np.mean(d_ab[candidate]))
    info["changed_ab_ratio"] = float(np.count_nonzero(changed_ab & candidate)) / float(candidate_count)
    info["combined_ratio"] = float(np.count_nonzero(changed_combined & candidate)) / float(candidate_count)
    min_mean_ab = max(0.0, float(getattr(args, "empty_change_min_mean_ab_diff", 4.5)))
    min_changed_ratio = max(0.0, float(getattr(args, "empty_change_min_ratio", 0.035)))
    min_combined_ratio = max(0.0, float(getattr(args, "empty_change_min_combined_ratio", 0.035)))

    background_like = (
        info["mean_ab_diff"] < min_mean_ab
        and info["changed_ab_ratio"] < min_changed_ratio
        and info["combined_ratio"] < min_combined_ratio
    )
    info["active"] = True
    if background_like:
        info.update({
            "accepted": False,
            "rejected": True,
            "reason": (
                "background-like YOLO candidate "
                f"meanAB={info['mean_ab_diff']:.2f} "
                f"abRatio={info['changed_ab_ratio']:.3f} "
                f"combinedRatio={info['combined_ratio']:.3f}"
            ),
        })
        return None, info

    info["reason"] = "accepted by empty-board change evidence"
    if not bool(getattr(args, "empty_refine_mask", True)):
        return mask, info

    dilate_px = max(1, int(getattr(args, "empty_refine_dilate_px", 11))) | 1
    dilate_kernel = cv2.getStructuringElement(cv2.MORPH_ELLIPSE, (dilate_px, dilate_px))
    support = cv2.dilate(changed, dilate_kernel, iterations=1)
    refined = cv2.bitwise_and(mask, support)
    refined = cv2.morphologyEx(refined, cv2.MORPH_CLOSE, morph_kernel, iterations=1)
    keep_ratio = float(np.count_nonzero(refined)) / float(candidate_count)
    info["refined_keep_ratio"] = keep_ratio
    min_keep = float(np.clip(getattr(args, "empty_refine_min_keep_ratio", 0.25), 0.0, 1.0))
    min_area = max(1, int(getattr(args, "empty_refine_min_area_px", 1200)))
    if keep_ratio >= min_keep and int(np.count_nonzero(refined)) >= min_area:
        info.update({"refined": True, "reason": f"accepted and refined keep={keep_ratio:.3f}"})
        return refined, info

    info["reason"] = f"accepted; refinement skipped keep={keep_ratio:.3f} < {min_keep:.3f}"
    return mask, info


def infer_bottoms_mask(seg_model, frame: np.ndarray, H: Optional[np.ndarray], imgsz: int, conf: float,
                       target_class_names: Sequence[str] = ("bottoms",), args=None) -> Tuple[Optional[BottomMaskBoard], str]:
    if args is not None:
        args._empty_baseline_last_info = {
            "enabled": bool(getattr(args, "empty_baseline_veto", True)),
            "available": getattr(args, "_empty_baseline_bgr", None) is not None,
            "active": False,
            "accepted": False,
            "reason": "segmentation not evaluated",
        }
        args._board_roi_last_info = {
            "enabled": bool(getattr(args, "board_roi", True)),
            "valid": False,
            "accepted": False,
            "reason": "segmentation not evaluated",
        }
    if seg_model is None:
        return None, "segmentation model is None"
    if H is None:
        return None, "Homography not locked"
    try:
        result = seg_model.predict(source=frame, imgsz=int(imgsz), conf=float(conf), retina_masks=True, verbose=False)[0]
    except Exception as e:
        return None, f"seg predict error: {repr(e)}"

    if getattr(result, "boxes", None) is None or result.boxes is None or len(result.boxes) == 0:
        return None, "no segmentation boxes"

    targets = parse_class_names(target_class_names) or ["bottoms"]
    allow_all = "*" in targets or "all" in targets
    target_set = set(targets)
    target_rank = {name: idx for idx, name in enumerate(targets)}
    names = getattr(result, "names", {}) or {}
    best = None
    best_rank = 10**6
    best_score = -1.0
    best_reason = f"no configured clothing class mask: {','.join(targets)}"
    for i in range(len(result.boxes)):
        cls_id = int(result.boxes.cls[i].item())
        cls_name = str(names.get(cls_id, cls_id))
        cls_id_name = str(cls_id)
        if not allow_all and cls_name not in target_set and cls_id_name not in target_set:
            continue
        c = float(result.boxes.conf[i].item())
        mask = result_mask_to_u8(result, i, frame.shape)
        if mask is None:
            best_reason = f"{cls_name} has no mask"
            continue
        empty_info: Dict[str, Any] = {}
        board_info: Dict[str, Any] = {}
        if args is not None:
            mask, empty_info = evaluate_empty_baseline_candidate(frame, mask, H, args)
            args._empty_baseline_last_info = dict(empty_info)
            if mask is None:
                best_reason = f"{cls_name} rejected by empty baseline: {empty_info.get('reason', 'background-like')}"
                continue
            mask, board_info = sanitize_board_mask_u8(
                mask, H, frame.shape, args, pose=None, require_pose=False, select_component=False,
            )
            args._board_roi_last_info = dict(board_info)
            if mask is None:
                best_reason = f"{cls_name} rejected by board ROI: {board_info.get('reason', 'outside board')}"
                continue
        contours, _ = cv2.findContours(mask, cv2.RETR_EXTERNAL, cv2.CHAIN_APPROX_SIMPLE)
        if not contours:
            best_reason = f"{cls_name} mask has no contour"
            continue
        contour = max(contours, key=cv2.contourArea)
        area = float(cv2.contourArea(contour))
        if area <= 1.0:
            best_reason = f"{cls_name} mask area too small"
            continue
        M = cv2.moments(contour)
        if abs(M["m00"]) > 1e-6:
            center_px = np.asarray([M["m10"] / M["m00"], M["m01"] / M["m00"]], dtype=np.float32)
        else:
            center_px = contour.reshape(-1, 2).astype(np.float32).mean(axis=0)
        bx, by = pixel_to_board(H, float(center_px[0]), float(center_px[1]))
        hull = cv2.convexHull(contour)
        hull_area = float(cv2.contourArea(hull))
        solidity = area / hull_area if hull_area > 1.0 else 0.0
        item = BottomMaskBoard(
            mask_u8=mask,
            contour=contour,
            area_px=area,
            center_px=center_px,
            center_board=np.asarray([bx, by], dtype=np.float32),
            class_name=cls_name,
            confidence=c,
            solidity=float(solidity),
            empty_baseline_info=dict(empty_info),
            board_roi_info=dict(board_info),
        )
        rank = target_rank.get(cls_name, target_rank.get(cls_id_name, len(targets)))
        score = area * max(c, 0.05) * max(solidity, 0.20)
        if best is None or rank < best_rank or (rank == best_rank and score > best_score):
            best = item
            best_rank = rank
            best_score = score
    if best is None:
        return None, best_reason
    if best_rank == 0:
        return best, "OK"
    return best, f"OK fallback clothing class={best.class_name}"


def suppress_specular_reflections(
        frame: np.ndarray, garment_mask: Optional[np.ndarray], args,
) -> Tuple[np.ndarray, Dict[str, Any]]:
    """Repair compact local highlights before pose/Heatmap inference.

    A bright table or an ArUco white cell is not automatically glare. A pixel
    must be bright relative to its own neighborhood, and connected components
    that are too large are rejected. When a garment mask is available, only
    highlights inside that mask are repaired.
    """
    info: Dict[str, Any] = {
        "enabled": bool(getattr(args, "glare_suppression", True)),
        "applied": False,
        "pixel_count": 0,
        "ratio": 0.0,
        "component_count": 0,
        "source": "garment" if garment_mask is not None else "frame",
        "mask_u8": None,
    }
    if frame is None or not info["enabled"]:
        return frame, info

    hsv = cv2.cvtColor(frame, cv2.COLOR_BGR2HSV)
    value = hsv[:, :, 2].astype(np.float32)
    saturation = hsv[:, :, 1].astype(np.float32)
    blur_k = odd_kernel_size(getattr(args, "glare_local_blur_ksize", 31), 9)
    local_base = cv2.GaussianBlur(value, (blur_k, blur_k), 0)
    local_rise = value - local_base

    value_min = float(getattr(args, "glare_value_min", 218.0))
    rise_min = float(getattr(args, "glare_local_rise_min", 24.0))
    saturation_max = float(getattr(args, "glare_saturation_max", 125.0))
    hard_value = float(getattr(args, "glare_hard_value", 250.0))
    candidate = (
        (value >= value_min)
        & (local_rise >= rise_min)
        & ((saturation <= saturation_max) | (value >= hard_value))
    )

    h, w = frame.shape[:2]
    if garment_mask is not None and np.asarray(garment_mask).shape[:2] == (h, w):
        support = np.asarray(garment_mask, dtype=np.uint8) > 0
    else:
        support = np.zeros((h, w), dtype=bool)
        margin_x = max(1, int(round(0.06 * w)))
        margin_y = max(1, int(round(0.06 * h)))
        support[margin_y:h - margin_y, margin_x:w - margin_x] = True
    candidate &= support

    raw = candidate.astype(np.uint8) * 255
    raw = cv2.morphologyEx(
        raw, cv2.MORPH_CLOSE,
        cv2.getStructuringElement(cv2.MORPH_ELLIPSE, (3, 3)),
        iterations=1,
    )
    count, labels, stats, _ = cv2.connectedComponentsWithStats(raw, connectivity=8)
    filtered = np.zeros_like(raw)
    support_area = max(1, int(np.count_nonzero(support)))
    min_area = max(2, int(getattr(args, "glare_component_min_area_px", 6)))
    max_area = max(
        min_area,
        int(round(support_area * float(getattr(
            args, "glare_component_max_area_ratio", 0.035,
        )))),
    )
    kept = 0
    for label in range(1, int(count)):
        area = int(stats[label, cv2.CC_STAT_AREA])
        width = int(stats[label, cv2.CC_STAT_WIDTH])
        height = int(stats[label, cv2.CC_STAT_HEIGHT])
        if area < min_area or area > max_area:
            continue
        if width > int(0.45 * w) or height > int(0.45 * h):
            continue
        filtered[labels == label] = 255
        kept += 1

    pixel_count = int(cv2.countNonZero(filtered))
    ratio = float(pixel_count) / float(support_area)
    info.update({
        "pixel_count": pixel_count,
        "ratio": ratio,
        "component_count": int(kept),
        "mask_u8": filtered,
    })
    min_ratio = max(0.0, float(getattr(args, "glare_min_apply_ratio", 0.00008)))
    if pixel_count == 0 or ratio < min_ratio:
        return frame, info

    dilate_px = max(0, int(getattr(args, "glare_inpaint_dilate_px", 2)))
    repair_mask = filtered
    if dilate_px > 0:
        k = 2 * dilate_px + 1
        repair_mask = cv2.dilate(
            repair_mask,
            cv2.getStructuringElement(cv2.MORPH_ELLIPSE, (k, k)),
            iterations=1,
        )
        repair_mask[~support] = 0
    radius = max(1.0, float(getattr(args, "glare_inpaint_radius_px", 4.0)))
    corrected = cv2.inpaint(frame, repair_mask, radius, cv2.INPAINT_TELEA)
    info["applied"] = True
    info["repair_mask_u8"] = repair_mask
    return corrected, info


def odd_kernel_size(value: Any, minimum: int = 3) -> int:
    k = max(int(value), int(minimum))
    if k % 2 == 0:
        k += 1
    return k


def normalize_masked_u8(values: np.ndarray, mask_u8: np.ndarray,
                        low_percentile: float = 2.0, high_percentile: float = 98.0,
                        min_range: float = 1e-6) -> np.ndarray:
    arr = np.asarray(values, dtype=np.float32)
    valid = mask_u8 > 0
    out = np.zeros(arr.shape[:2], dtype=np.uint8)
    if not np.any(valid):
        return out
    vals = arr[valid]
    lo = float(np.percentile(vals, low_percentile))
    hi = float(np.percentile(vals, high_percentile))
    if not np.isfinite(lo) or not np.isfinite(hi):
        return out
    span = max(float(min_range), hi - lo)
    scaled = (arr - lo) * (255.0 / span)
    out = np.clip(scaled, 0, 255).astype(np.uint8)
    out[~valid] = 0
    return out


def build_local_shadow_map(frame: np.ndarray, inner_mask: np.ndarray, args) -> Dict[str, Any]:
    """Measure locally dark fold shadows without requiring a globally bright garment."""
    lab = cv2.cvtColor(frame, cv2.COLOR_BGR2LAB)
    luminance = lab[:, :, 0].astype(np.float32)
    blur_k = odd_kernel_size(getattr(args, "wrinkle_shadow_blur_ksize", 51), 9)
    local_base = cv2.GaussianBlur(luminance, (blur_k, blur_k), 0)
    raw = np.maximum(local_base - luminance, 0.0)
    raw[inner_mask == 0] = 0.0

    values = raw[inner_mask > 0]
    if values.size:
        p90 = float(np.percentile(values, 90.0))
        p98 = float(np.percentile(values, 98.0))
        p995 = float(np.percentile(values, 99.5))
    else:
        p90 = p98 = p995 = 0.0
    min_scale = max(1.0, float(getattr(args, "wrinkle_shadow_min_scale_raw", 8.0)))
    scale = max(min_scale, p995)
    normalized = np.clip(raw * (255.0 / scale), 0.0, 255.0).astype(np.uint8)
    normalized[inner_mask == 0] = 0
    support_threshold = max(
        float(getattr(args, "wrinkle_shadow_support_raw_min", 3.0)),
        p90,
    )
    return {
        "raw": raw,
        "normalized": normalized,
        "scale_raw": float(scale),
        "p90_raw": p90,
        "p98_raw": p98,
        "p995_raw": p995,
        "support_raw_threshold": float(support_threshold),
    }


def classify_wrinkle_geometry(area_px: float, mask_area_px: float,
                              major_length_px: float, minor_length_px: float,
                              edge_distance_px: float, shadow_mean: float,
                              shadow_max: float, shadow_support: float,
                              args) -> Dict[str, Any]:
    """Classify action geometry while keeping weak/fine candidates for finish checks."""
    linearity = float(major_length_px / max(1.0, minor_length_px))
    area_ratio = float(area_px / max(1.0, mask_area_px))
    edge_limit = float(getattr(args, "wrinkle_type_edge_distance_px", 15.0))
    long_linearity = float(getattr(args, "wrinkle_type_long_linearity", 2.60))
    short_linearity = float(getattr(args, "wrinkle_type_short_linearity", 1.65))
    long_length = float(getattr(args, "wrinkle_type_long_length_px", 65.0))
    short_length = float(getattr(args, "wrinkle_type_short_length_px", 32.0))

    if edge_distance_px <= edge_limit:
        wrinkle_type = "EDGE"
        pull_scale = float(getattr(args, "wrinkle_type_edge_pull_scale", 0.72))
    elif linearity >= long_linearity and major_length_px >= long_length:
        wrinkle_type = "LONG_LINEAR"
        pull_scale = float(getattr(args, "wrinkle_type_long_pull_scale", 1.15))
    elif linearity >= short_linearity and major_length_px >= short_length:
        wrinkle_type = "SHORT_LINEAR"
        pull_scale = float(getattr(args, "wrinkle_type_short_pull_scale", 0.78))
    else:
        wrinkle_type = "BROAD_ROUND"
        pull_scale = float(getattr(args, "wrinkle_type_round_pull_scale", 0.62))

    strong_size = bool(
        area_px >= float(getattr(args, "wrinkle_tier_strong_area_px", 220.0))
        or area_ratio >= float(getattr(args, "wrinkle_tier_strong_area_ratio", 0.0015))
    )
    strong_length = bool(major_length_px >= float(getattr(args, "wrinkle_tier_strong_length_px", 72.0)))
    medium_size = bool(
        area_px >= float(getattr(args, "wrinkle_tier_medium_area_px", 110.0))
        or area_ratio >= float(getattr(args, "wrinkle_tier_medium_area_ratio", 0.0008))
    )
    shadow_supported = bool(
        (shadow_mean >= float(getattr(args, "wrinkle_tier_shadow_mean", 22.0))
         or shadow_max >= float(getattr(args, "wrinkle_tier_shadow_max", 70.0)))
        and shadow_support >= float(getattr(args, "wrinkle_tier_shadow_support", 0.06))
    )
    if strong_size and strong_length:
        tier, tier_name = 3, "LARGE_LONG"
    elif strong_size or strong_length:
        tier, tier_name = 2, "LARGE_OR_LONG"
    else:
        tier, tier_name = 1, "FINE_OR_LOCAL"
    if shadow_supported:
        tier_name += "_DARK"

    return {
        "wrinkle_type": wrinkle_type,
        "pull_scale": float(np.clip(pull_scale, 0.35, 1.40)),
        "priority_tier": int(tier),
        "priority_tier_name": tier_name,
        "area_ratio": area_ratio,
        "shadow_supported": shadow_supported,
        "medium_size": medium_size,
    }
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
