ChoBeomGyu25/2026ESWContest_free_-/SW/Jetson/preprocessing/lower/dual/undistort/50-1.py

#!/usr/bin/env python3
# -*- coding: utf-8 -*-
"""Standalone 5-point basket calibration and temporary grasp-point viewer.

Five-point order (fixed):
  P0/V0: visible corner adjacent to the hidden corner on edge A
  P1/V1: visible corner diagonally opposite the hidden corner
  P2/V2: other visible corner adjacent to the hidden corner on edge B
  P3/E0: visible point on straight edge H-V0
  P4/E2: visible point on straight edge H-V2

The hidden corner H is reconstructed as intersection(line(V0,E0), line(V2,E2)).
Basket corner order is H -> V0 -> V1 -> V2. The temporary grasp point is
intersection(diagonal(H,V1), diagonal(V0,V2)).

Keys:
  B       enter/leave basket mode (terminal or OpenCV window)
  C       start/restart calibration (ARM2 torque off)
  click   select current image point
  Enter   save ARM2 T:105 feedback for pending click
  U       cancel pending click, otherwise undo last point
  S       recompute and save JSON (requires 5 points)
  L       reload JSON
  F       ARM2 feedback
  T / N   ARM2 torque off / on
  G       open gripper
  H       prepare ARM2 hover plan above temporary grasp point
  D       prepare torque-monitored descent after hover
  Enter   execute a prepared hover or descent action
  Q/ESC   quit

This file calibrates, visualizes, performs an ARM2-only hover, descends with
shoulder-primary robust contact detection, and—only after confirmed cloth
contact—automatically opens wider, closes the gripper, and lifts vertically.
After the adaptive vertical lift either reaches its preferred height or detects
a real vertical saturation, the last measured Z is accepted as the transit Z.
No second absolute-Z clearance gate is applied after saturation. From that exact
pose it sends one direct T:104 goal to the folding-board center, judges arrival
by XY only, opens the gripper there, and returns ARM2 to the A150 taught standby
pose. It never sends a command to ARM1.

Hover safety sequence:
  H       prepare a hover plan from the loaded 5-point JSON
  Enter   execute the prepared hover plan

Terminal logging:
  Every Python stdout/stderr message is mirrored live to a timestamped UTF-8
  text file. Native execution writes to /home/deca/project_train/aruco_test/dual.
  Docker execution automatically uses the persistent /workspace mirror.

Execution path:
  1) Read the current ARM2 pose with T:105.
  2) If ARM2 is already at the A150 taught standby pose, first raise vertically
     to the configured board safe-hover Z and move to the calibrated ARM2
     board-inner (RED_EXTRA) waypoint. The basket command is blocked until
     that board-safe waypoint is actually reached.
  3) Move horizontally from the board-safe waypoint to the temporary basket
     grasp XY at the same high transit Z. For non-standby starts, retain the
     original direct high-Z basket approach.
  4) Descend vertically only after reaching the target XY.

The five-point Z mean is used as the hover reference. For collision safety,
the final hover Z is also constrained to remain above the highest calibrated
rim point by a configurable minimum clearance.
"""

import argparse
import atexit
import csv
import json
import math
import os
import platform
import select
import shutil
import statistics
import sys
import threading
import time
import traceback
from pathlib import Path
from dataclasses import dataclass
from datetime import datetime
from typing import Any, Dict, List, Optional, Sequence, Tuple, Union

os.environ["QT_X11_NO_MITSHM"] = "1"
os.environ["GDK_DISABLE_SHM"] = "1"
os.environ.setdefault("NO_AT_BRIDGE", "1")

import cv2
import numpy as np

try:
    import serial
except Exception:
    serial = None

try:
    import termios
    import tty
except Exception:
    termios = None
    tty = None

BUILD_ID = "D50-BASKET-DIRECT-AIR-DROP-20260813"

POINT_SPECS = (
    ("P0_V0", "visible corner adjacent to hidden corner on edge A"),
    ("P1_V1", "visible corner diagonally opposite the hidden corner"),
    ("P2_V2", "other visible corner adjacent to hidden corner on edge B"),
    ("P3_E0", "point on straight edge H-V0; avoid rounded corner"),
    ("P4_E2", "point on straight edge H-V2; avoid rounded corner"),
)


SESSION_LOG_REQUESTED_DIR = Path("/home/deca/project_train/aruco_test/dual")
SESSION_LOG_DOCKER_MIRROR_DIR = Path("/workspace/project_train/aruco_test/dual")


class _TeeTextStream:
    """Write each Python stdout/stderr message to the terminal and a UTF-8 log file."""

    def __init__(self, terminal_stream, log_stream, lock: threading.RLock):
        self._terminal_stream = terminal_stream
        self._log_stream = log_stream
        self._lock = lock

    def write(self, text):
        if not isinstance(text, str):
            text = str(text)
        with self._lock:
            terminal_result = self._terminal_stream.write(text)
            self._log_stream.write(text)
            # Line-buffered file plus explicit flush prevents long-run data loss.
            self._log_stream.flush()
            return terminal_result

    def flush(self):
        with self._lock:
            self._terminal_stream.flush()
            self._log_stream.flush()

    def isatty(self):
        return bool(getattr(self._terminal_stream, "isatty", lambda: False)())

    def fileno(self):
        return self._terminal_stream.fileno()

    @property
    def encoding(self):
        return getattr(self._terminal_stream, "encoding", "utf-8")

    @property
    def errors(self):
        return getattr(self._terminal_stream, "errors", "replace")

    def __getattr__(self, name):
        return getattr(self._terminal_stream, name)


class SessionTerminalLog:
    """Mirror the complete Python terminal session to a timestamped text file."""

    def __init__(self):
        self._original_stdout = sys.stdout
        self._original_stderr = sys.stderr
        self._log_stream = None
        self._lock = threading.RLock()
        self.path: Optional[Path] = None
        self.requested_dir = SESSION_LOG_REQUESTED_DIR
        self.used_docker_mirror = False
        self._closed = False

    @staticmethod
    def _is_writable_directory(path: Path) -> bool:
        return path.is_dir() and os.access(str(path), os.W_OK)

    def _resolve_directory(self) -> Path:
        # On the host, use the exact directory requested by the operator.
        if self._is_writable_directory(self.requested_dir):
            return self.requested_dir

        # The project is normally mounted into Docker as /workspace/project_train.
        # Writing there persists into the requested host project directory.
        if self._is_writable_directory(SESSION_LOG_DOCKER_MIRROR_DIR):
            self.used_docker_mirror = True
            return SESSION_LOG_DOCKER_MIRROR_DIR

        # Native execution may begin before the destination directory exists.
        self.requested_dir.mkdir(parents=True, exist_ok=True)
        if not self._is_writable_directory(self.requested_dir):
            raise PermissionError(f"session log directory is not writable: {self.requested_dir}")
        return self.requested_dir

    def start(self) -> Path:
        log_dir = self._resolve_directory()
        timestamp = datetime.now().strftime("%Y%m%d_%H%M%S_%f")
        filename = f"basket_v24_terminal_{timestamp}_pid{os.getpid()}.txt"
        self.path = log_dir / filename
        self._log_stream = self.path.open("x", encoding="utf-8", buffering=1)
        sys.stdout = _TeeTextStream(self._original_stdout, self._log_stream, self._lock)
        sys.stderr = _TeeTextStream(self._original_stderr, self._log_stream, self._lock)
        print("\n========== TERMINAL SESSION LOG STARTED ==========")
        print(f"[SESSION-LOG] file={self.path}")
        print(f"[SESSION-LOG] requested_host_dir={self.requested_dir}")
        if self.used_docker_mirror:
            print(
                "[SESSION-LOG] Docker mirror active: /workspace/project_train/... "
                "persists to the requested host project directory"
            )
        print(f"[SESSION-LOG] started_at={datetime.now().isoformat(timespec='seconds')}")
        print("==================================================\n")
        atexit.register(self.close)
        return self.path
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
